dragonet80/MultiMicro/Base/ARE_entrenadora_modular_Arduino_mod.brd

## EAGLE design Base/ARE_entrenadora_modular_Arduino_mod.brd (2015-02-18)

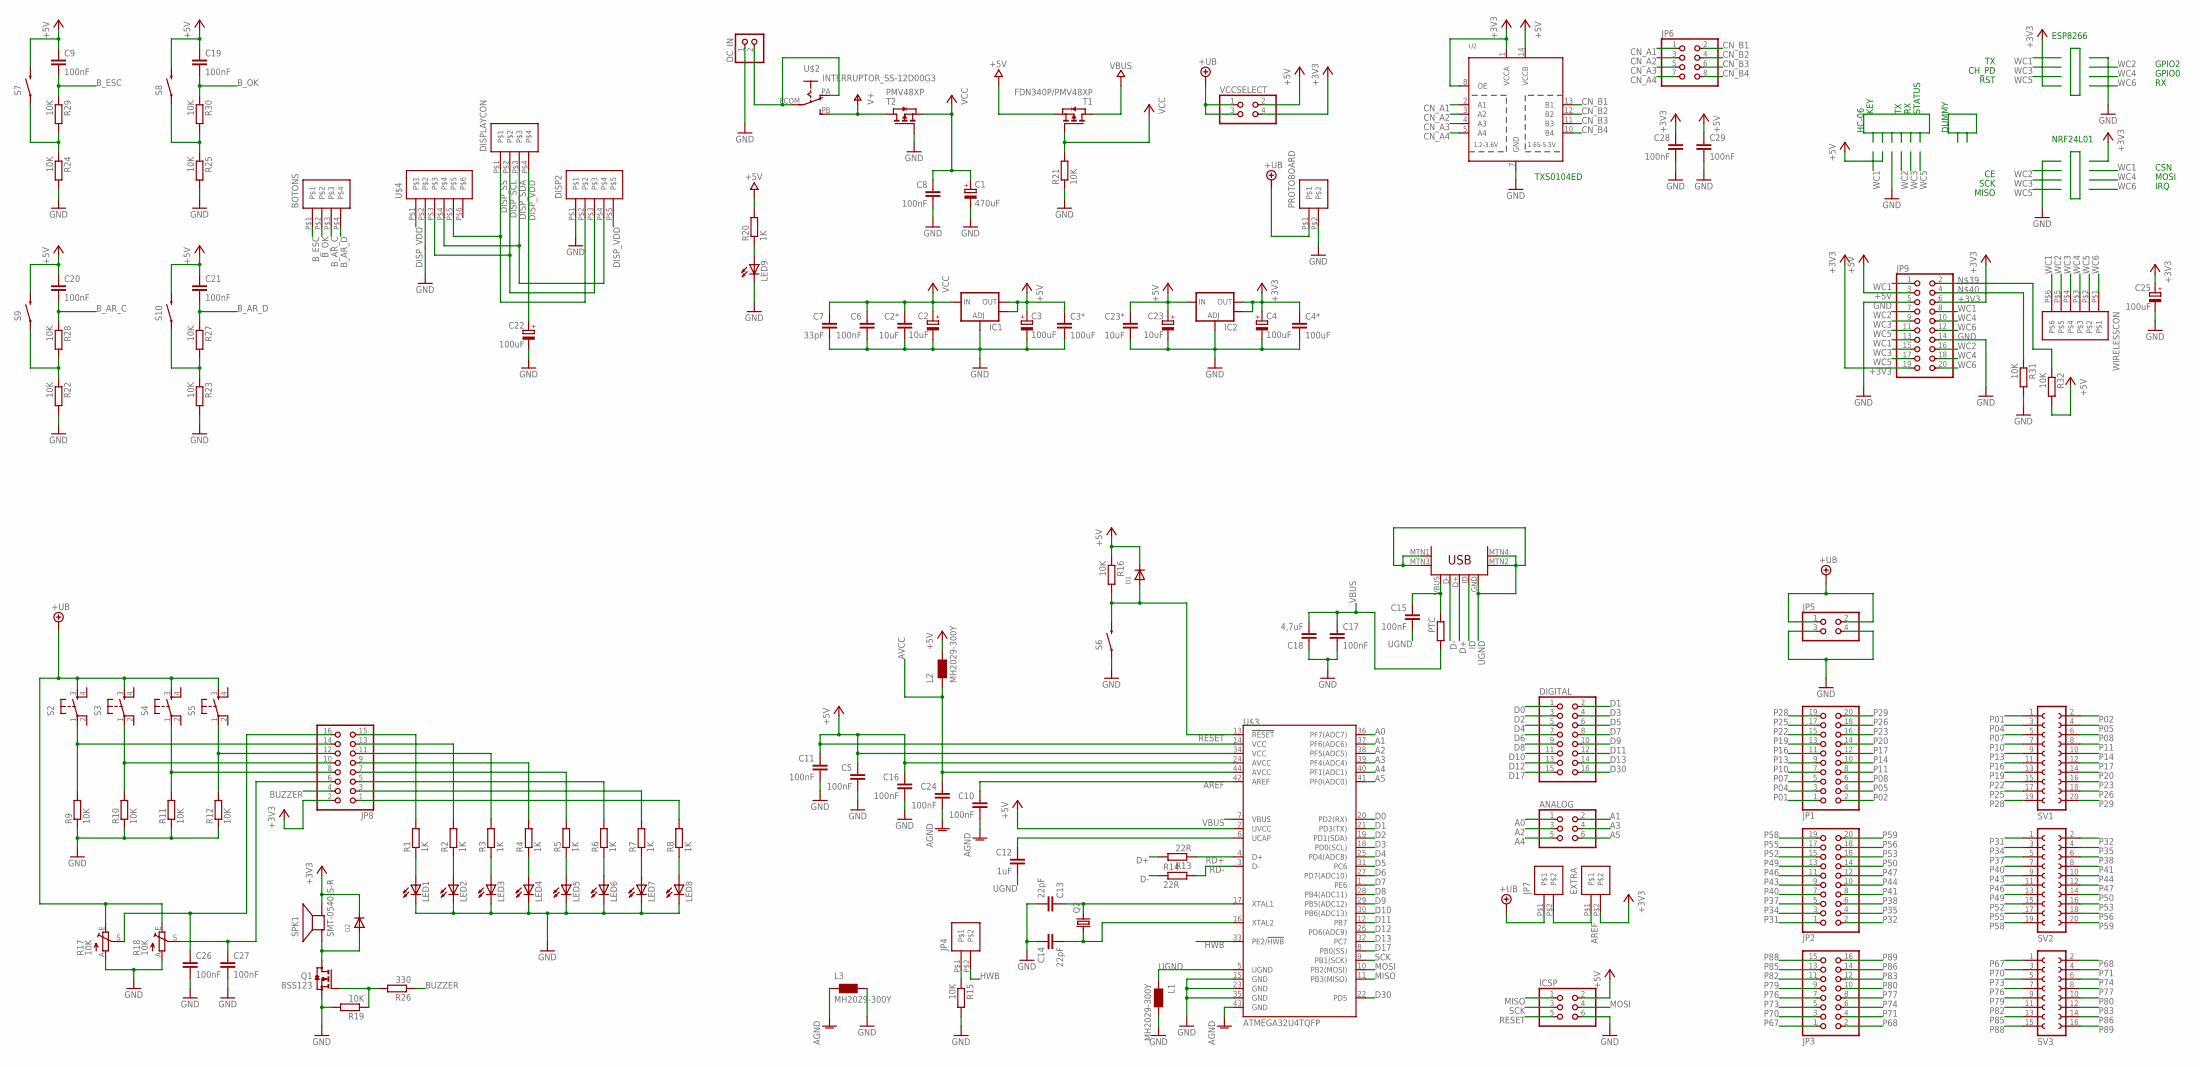
[picture p35: schematic ARE_entrenadora_modular_Arduino_mod.sch]

Parts:
ANALOG: PINHD-2X3; 2X03
BOTONS: PINHEAD_1X4; PINHEAD_1X4_2.54
C1: 470uF; E3,5-8
C2, C23: 10uF; SMC_C
C2*, C23*: 10uF; C1206
C3, C4: 100uF; CT7343
C3*, C4*: 100uF; C1206
C5, C6, C8, C9, C10, C11, C15, C16, C17, C19, C20, C21, C24, C26, C27, C28, C29: 100nF; C0805
C7: 33pF; C0805
C12: 1uF; C0805
C13, C14: 22pF; C0805
C18: 4,7uF; C0805
C22, C25: 100uF; SMC_C
D1, D2: DIODESOD-123; SOD-123
DC_IN: PINHD-1X2/90; 1X02/90
DIGITAL: PINHD-2X8; 2X08
DISP2: PINHEAD_1X5; PINHEAD_1X5_2.54
DISPLAYCON: PINHEAD_1X4; PINHEAD_1X4_2.54
EXTRA: PINHEAD_1X2; PINHEAD_1X2_2.54
IC1, IC2: V_REG_LM1117SOT223; SOT223
ICSP: PINHD-2X3; 2X03
JP1, JP2: PINHD-2X10/90; 2X10/90
JP3: PINHD-2X8/90; 2X08/90
JP4, JP7: PINHEAD_1X2; PINHEAD_1X2_2.54
JP5: PINHD-2X2/90; 2X02/90
JP6: PINHD-2X4; 2X04
JP8: PINHD-2X8; 2X08
JP9: PINHD-2X10; 2X10
L1, L2, L3: MH2029-300Y; 0805
LED1, LED2, LED3, LED4, LED5, LED6, LED7, LED8, LED9: LEDCHIP-LED0805; CHIP-LED0805
PROTOBOARD: PINHEAD_1X2; PINHEAD_1X2_2.54
PTC: R-EU_R1206; R1206
Q1: BSS123; SOT23
Q2: CRYSTALHC49UP; HC49UP
R1, R2, R3, R4, R5, R6, R7, R8, R20: 1K; R0805
R9, R10, R11, R12, R15, R16, R19, R21, R22, R23, R24, R25, R27, R28, R29, R30, R31, R32: 10K; R0805
R13, R14: 22R; R0805
R17, R18: 10K; CA6V
R26: 330; R0805
S2, S3, S4, S5: TAC_SWITCHPTH; TACTILE-PTH
S6, S7, S8, S9, S10: SWITCH-MOMENTARY-2-SMD-1101NE; TACTILE-SWITCH-1101NE
SPK1: SMT-0540-S-R
SV1, SV2: FE10-2
SV3: FE08-2
T1: FDN340P/PMV48XP; SOT-23
T2: PMV48XP; SOT-23
U2: TXB0104PWRSOIC14; SO14
U$1: USB-MINIB-5PIN; USB-MINIB
U$2: INTERRUPTOR_SS-12D00G3; SS-12D00G3
U$3: ATMEGA32U4TQFP; SPARKFUN-DIGITALIC_TQFP44
U$4: PINHEAD_1X6; PINHEAD_1X6_2.54
VCCSELECT: PINHD-2X2; 2X02
WIRELESSCON: PINHEAD_1X6; PINHEAD_1X6_2.54

Connections:
+3V3: C4.+, C4*.1, C25.+, C28.1, D2.C, EXTRA.P$2, IC2.2 (OUT), IC2.4 (OUT), JP8.2, JP9.6, JP9.19, SPK1.+ (-), U2.1 (VCCA), U2.8 (OE), VCCSELECT.4
+5V: C3.+, C3*.1, C5.1, C9.1, C11.1, C16.1, C19.1, C20.1, C21.1, C23.+, C23*.1, C29.1, D1.C, IC1.2 (OUT), IC1.4 (OUT), IC2.3 (IN), ICSP.2, JP9.3, L2.2, R16.1, R20.2, R32.2, S7.P$2 (2), S8.P$2 (2), S9.P$2 (2), S10.P$2 (2), T1.2 (S), U2.14 (VCCB), U$3.2 (UVCC), U$3.14 (VCC), U$3.24 (AVCC), U$3.34 (VCC), VCCSELECT.2
+UB: JP5.1, JP5.2, JP7.P$1, PROTOBOARD.P$1, R17.E, R18.E, S2.3, S3.3, S4.3, S5.3, VCCSELECT.1, VCCSELECT.3
A0: ANALOG.1, U$3.36 (PF7(ADC7))
A1: ANALOG.2, U$3.37 (PF6(ADC6))
A2: ANALOG.3, U$3.38 (PF5(ADC5))
A3: ANALOG.4, U$3.39 (PF4(ADC4))
A4: ANALOG.5, U$3.40 (PF1(ADC1))
A5: ANALOG.6, U$3.41 (PF0(ADC0))
AGND: C10.2, C24.2, L3.1, U$3.43 (GND)
AREF: C10.1, EXTRA.P$1, JP7.P$2, U$3.42 (AREF)
AVCC: C24.1, L2.1, U$3.44 (AVCC)
BUZZER: JP8.4, R26.1
B_AR_C: BOTONS.P$3, C20.2, R28.1
B_AR_D: BOTONS.P$4, C21.2, R27.1
B_ESC: BOTONS.P$1, C9.2, R29.1
B_OK: BOTONS.P$2, C19.2, R30.1
CN_A1: JP6.1, U2.2 (A1)
CN_A2: JP6.3, U2.3 (A2)
CN_A3: JP6.5, U2.4 (A3)
CN_A4: JP6.7, U2.5 (A4)
CN_B1: JP6.2, U2.13 (B1)
CN_B2: JP6.4, U2.12 (B2)
CN_B3: JP6.6, U2.11 (B3)
CN_B4: JP6.8, U2.10 (B4)
D0: DIGITAL.1, U$3.20 (PD2(RX))
D1: DIGITAL.2, U$3.21 (PD3(TX))
D2: DIGITAL.3, U$3.19 (PD1(SDA))
D3: DIGITAL.4, U$3.18 (PD0(SCL))
D4: DIGITAL.5, U$3.25 (PD4(ADC8))
D5: DIGITAL.6, U$3.31 (PC6)
D6: DIGITAL.7, U$3.27 (PD7(ADC10))
D7: DIGITAL.8, U$3.1 (PE6)
D8: DIGITAL.9, U$3.28 (PB4(ADC11))
D9: DIGITAL.10, U$3.29 (PB5(ADC12))
D10: DIGITAL.11, U$3.30 (PB6(ADC13))
D11: DIGITAL.12, U$3.12 (PB7)
D12: DIGITAL.13, U$3.26 (PD6(ADC9))
D13: DIGITAL.14, U$3.32 (PC7)
D17: DIGITAL.15, U$3.8 (PB0(SS))
D30: DIGITAL.16, U$3.22 (PD5)
D+: R13.2, U$1.D+
D-: R14.1, U$1.D-
DISP_SCL: DISP2.P$3, DISPLAYCON.P$2, U$4.P$3
DISP_SDA: DISP2.P$4, DISPLAYCON.P$3, U$4.P$4
DISP_SS: DISP2.P$2, DISPLAYCON.P$1, U$4.P$5
DISP_VDD: C22.+, DISP2.P$5, DISPLAYCON.P$4, U$4.P$1
GND: C1.-, C2.-, C2*.2, C3.-, C3*.2, C4.-, C4*.2, C5.2, C6.2, C7.2, C8.2, C11.2, C13.2, C14.1, C16.2, C17.2, C18.1, C22.-, C23.-, C23*.2, C25.-, C26.2, C27.2, C28.2, C29.2, DC_IN.1, DISP2.P$1, IC1.1 (ADJ), IC2.1 (ADJ), ICSP.6, JP5.3, JP5.4, JP9.5, JP9.14, L1.2, L3.2, LED1.C, LED2.C, LED3.C, LED4.C, LED5.C, LED6.C, LED7.C, LED8.C, LED9.C, PROTOBOARD.P$2, Q1.2 (S), R9.1, R10.1, R11.1, R12.1, R15.2, R17.A, R18.A, R19.2, R21.1, R22.2, R23.2, R24.2, R25.2, R31.2, S6.P$1 (1), T2.3 (G), U2.7 (GND), U$3.15 (GND), U$3.23 (GND), U$3.35 (GND), U$4.P$2
HWB: JP4.P$2, U$3.33 (PE2/!HWB)
ID: U$1.ID
MISO: ICSP.1, U$3.11 (PB3(MISO))
MOSFET_BASE: Q1.1 (G), R19.1, R26.2
MOSI: ICSP.4, U$3.10 (PB2(MOSI))
unnamed: LED1.A, R1.1
unnamed: LED2.A, R2.1
unnamed: LED3.A, R3.1
unnamed: LED4.A, R4.1
unnamed: JP8.13, R2.2
unnamed: JP8.11, R3.2
unnamed: JP8.15, R1.2
unnamed: JP8.9, R4.2
unnamed: LED9.A, R20.1
unnamed: C27.1, JP8.6, R18.S
unnamed: D2.A, Q1.3 (D), SPK1.- (+)
unnamed: JP4.P$1, R15.1
unnamed: C13.1, Q2.2, U$3.17 (XTAL1)
unnamed: C14.2, Q2.1, U$3.16 (XTAL2)
unnamed: R22.1, R28.2, S9.P$1 (1)
unnamed: JP8.8, R11.2, S4.1
unnamed: JP8.12, R12.2, S5.1
unnamed: C15.1, PTC.1, U$1.VBUS
unnamed: R24.1, R29.2, S7.P$1 (1)
unnamed: LED5.A, R5.1
unnamed: R25.1, R30.2, S8.P$1 (1)
unnamed: JP8.10, R10.2, S3.1
unnamed: R23.1, R27.2, S10.P$1 (1)
unnamed: C12.1, U$3.6 (UCAP)
unnamed: JP9.2, R32.1
unnamed: JP9.4, R31.1
unnamed: DC_IN.2, U$2.PA, U$2.PCOM
unnamed: LED6.A, R6.1
unnamed: LED7.A, R7.1
unnamed: LED8.A, R8.1
unnamed: JP8.14, R9.2, S2.1
unnamed: C26.1, JP8.16, R17.S
unnamed: JP8.5, R6.2
unnamed: JP8.3, R7.2
unnamed: JP8.7, R5.2
unnamed: JP8.1, R8.2
P01: JP1.1, SV1.1
P02: JP1.2, SV1.2
P04: JP1.3, SV1.3
P05: JP1.4, SV1.4
P07: JP1.5, SV1.5
P08: JP1.6, SV1.6
P10: JP1.7, SV1.7
P11: JP1.8, SV1.8
P13: JP1.9, SV1.9
P14: JP1.10, SV1.10
P16: JP1.11, SV1.11
P17: JP1.12, SV1.12
P19: JP1.13, SV1.13
P20: JP1.14, SV1.14
P22: JP1.15, SV1.15
P23: JP1.16, SV1.16
P25: JP1.17, SV1.17
P26: JP1.18, SV1.18
P28: JP1.19, SV1.19
P29: JP1.20, SV1.20
P31: JP2.1, SV2.1
P32: JP2.2, SV2.2
P34: JP2.3, SV2.3
P35: JP2.4, SV2.4
P37: JP2.5, SV2.5
P38: JP2.6, SV2.6
P40: JP2.7, SV2.7
P41: JP2.8, SV2.8
P43: JP2.9, SV2.9
P44: JP2.10, SV2.10
P46: JP2.11, SV2.11
P47: JP2.12, SV2.12
P49: JP2.13, SV2.13
P50: JP2.14, SV2.14
P52: JP2.15, SV2.15
P53: JP2.16, SV2.16
P55: JP2.17, SV2.17
P56: JP2.18, SV2.18
P58: JP2.19, SV2.19
P59: JP2.20, SV2.20
P67: JP3.1, SV3.1
P68: JP3.2, SV3.2
P70: JP3.3, SV3.3
P71: JP3.4, SV3.4
P73: JP3.5, SV3.5
P74: JP3.6, SV3.6
P76: JP3.7, SV3.7
P77: JP3.8, SV3.8
P79: JP3.9, SV3.9
P80: JP3.10, SV3.10
P82: JP3.11, SV3.11
P83: JP3.12, SV3.12
P85: JP3.13, SV3.13
P86: JP3.14, SV3.14
P88: JP3.15, SV3.15
P89: JP3.16, SV3.16
RD+: R13.1, U$3.4 (D+)
RD-: R14.2, U$3.3 (D-)
RESET: D1.A, ICSP.5, R16.2, S6.P$2 (2), U$3.13 (!RESET)
SCK: ICSP.3, U$3.9 (PB1(SCK))
UGND: C12.2, C15.2, L1.1, U$1.GND, U$1.MTN1 (MTN2), U$1.MTN2 (MTN3), U$1.MTN3 (MTN1), U$1.MTN4, U$3.5 (UGND)
V+: T2.1 (D), U$2.PB
VBUS: C17.1, C18.2, PTC.2, T1.1 (D), U$3.7 (VBUS)
VCC: C1.+, C2.+, C2*.1, C6.1, C7.1, C8.1, IC1.3 (IN), R21.2, T1.3 (G), T2.2 (S)
WC1: JP9.1, JP9.8, JP9.13, WIRELESSCON.P$6
WC2: JP9.7, JP9.16, WIRELESSCON.P$5
WC3: JP9.9, JP9.15, WIRELESSCON.P$4
WC4: JP9.10, JP9.18, WIRELESSCON.P$3
WC5: JP9.11, JP9.17, WIRELESSCON.P$2
WC6: JP9.12, JP9.20, WIRELESSCON.P$1

Notes on the sheet:
TXS0104ED
KEY
STATUS
CH_PD
RST
SCK
MISO
GPIO2
GPIO0
CSN
MOSI
IRQ
HC-06
DUMMY
NRF24L01
ESP8266

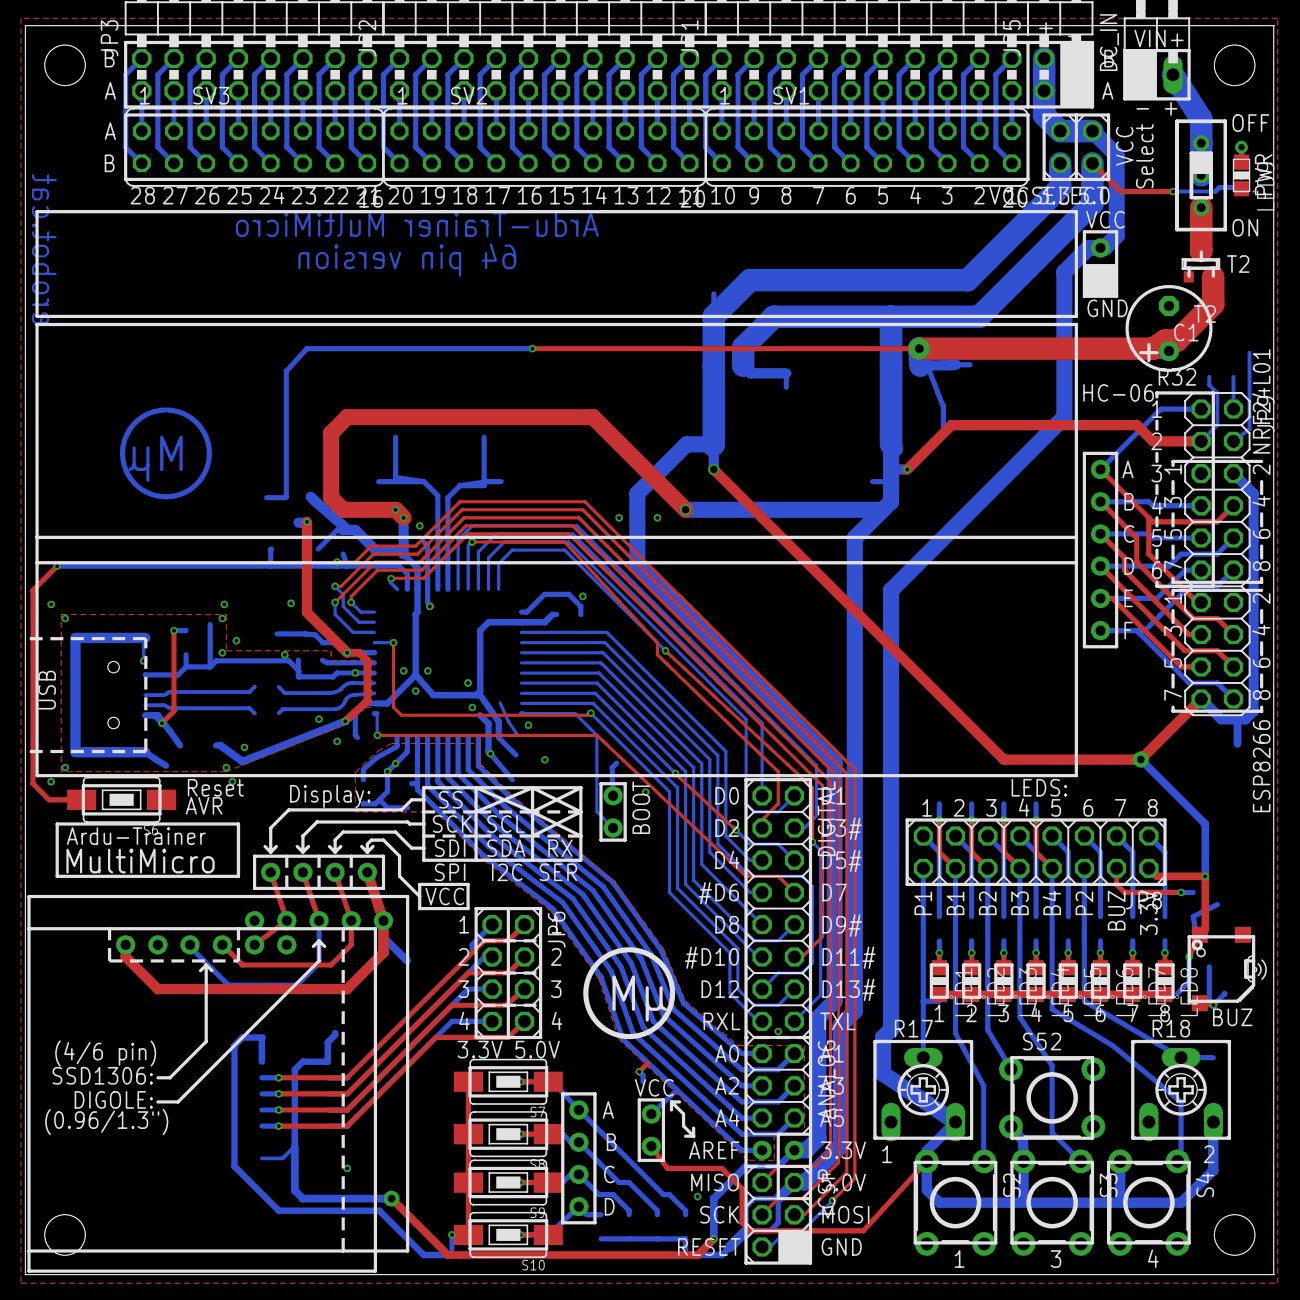
[picture p36: board ARE_entrenadora_modular_Arduino_mod.brd from above]

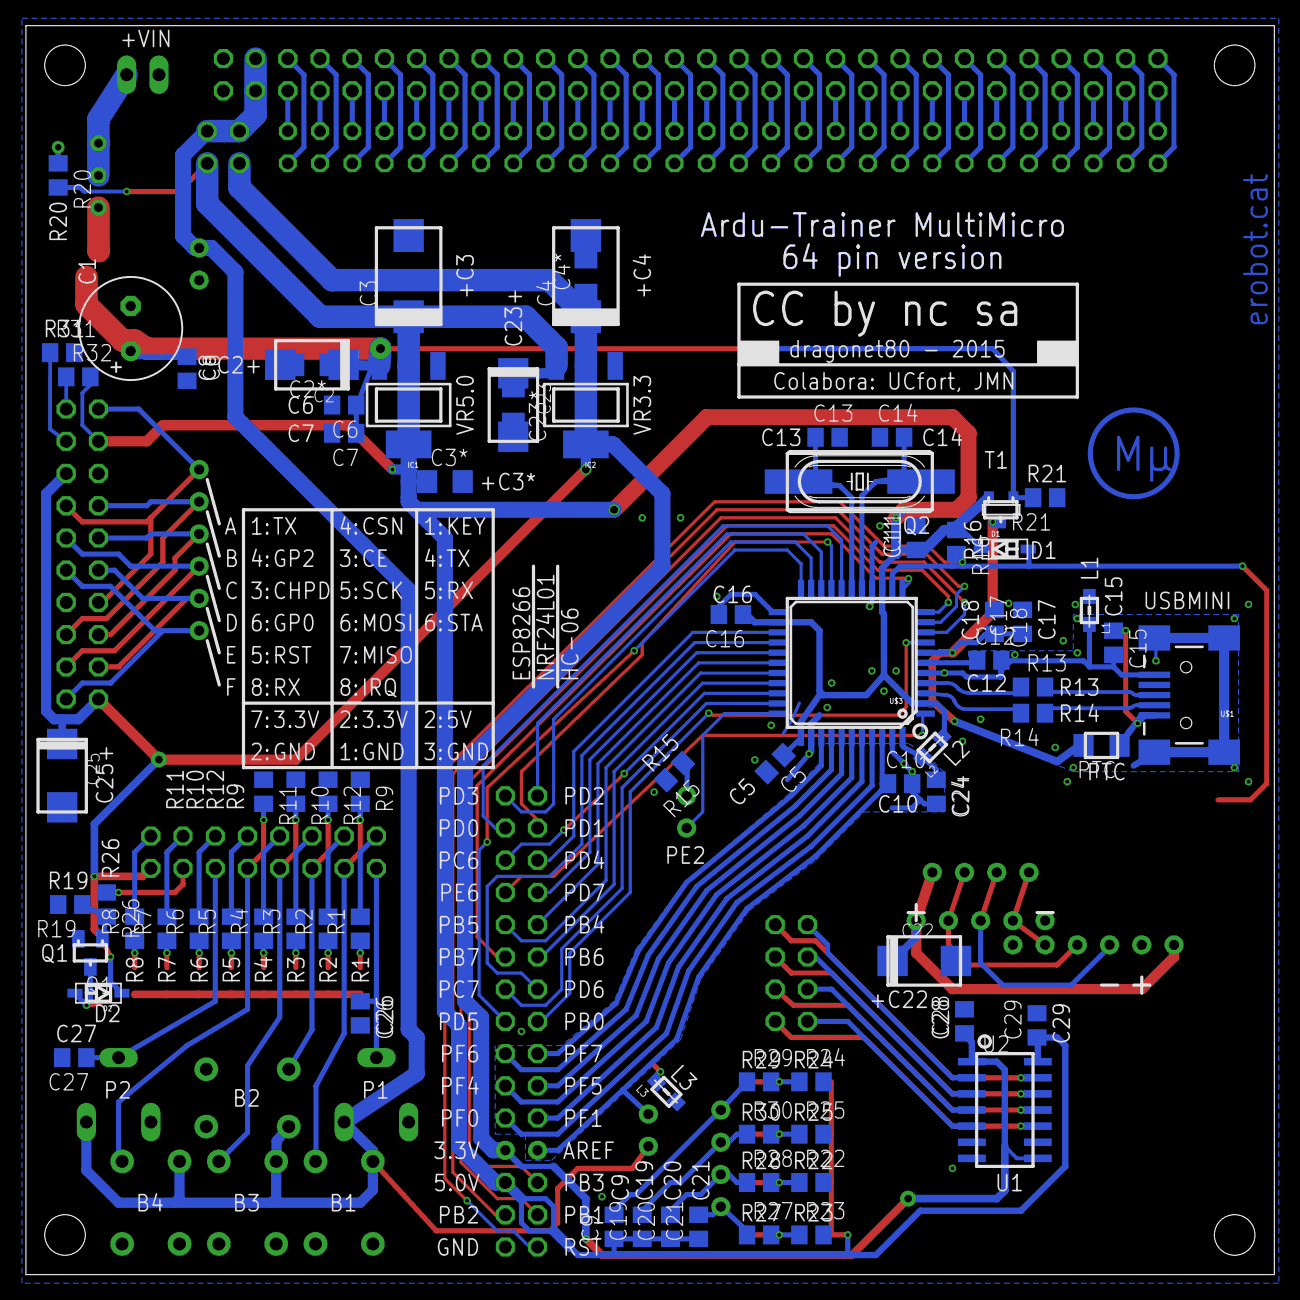
[picture p37: board ARE_entrenadora_modular_Arduino_mod.brd from below]

Board: 2 copper layers, 98.4 x 98.5 mm, 124 parts (77 on the bottom side), 158 nets.
