dragonet80/MultiMicro/Adaptadores/Microchip/ARE_adaptadora_PIC_44pin.brd

## EAGLE design Adaptadores/Microchip/ARE_adaptadora_PIC_44pin.brd (2015-02-18)

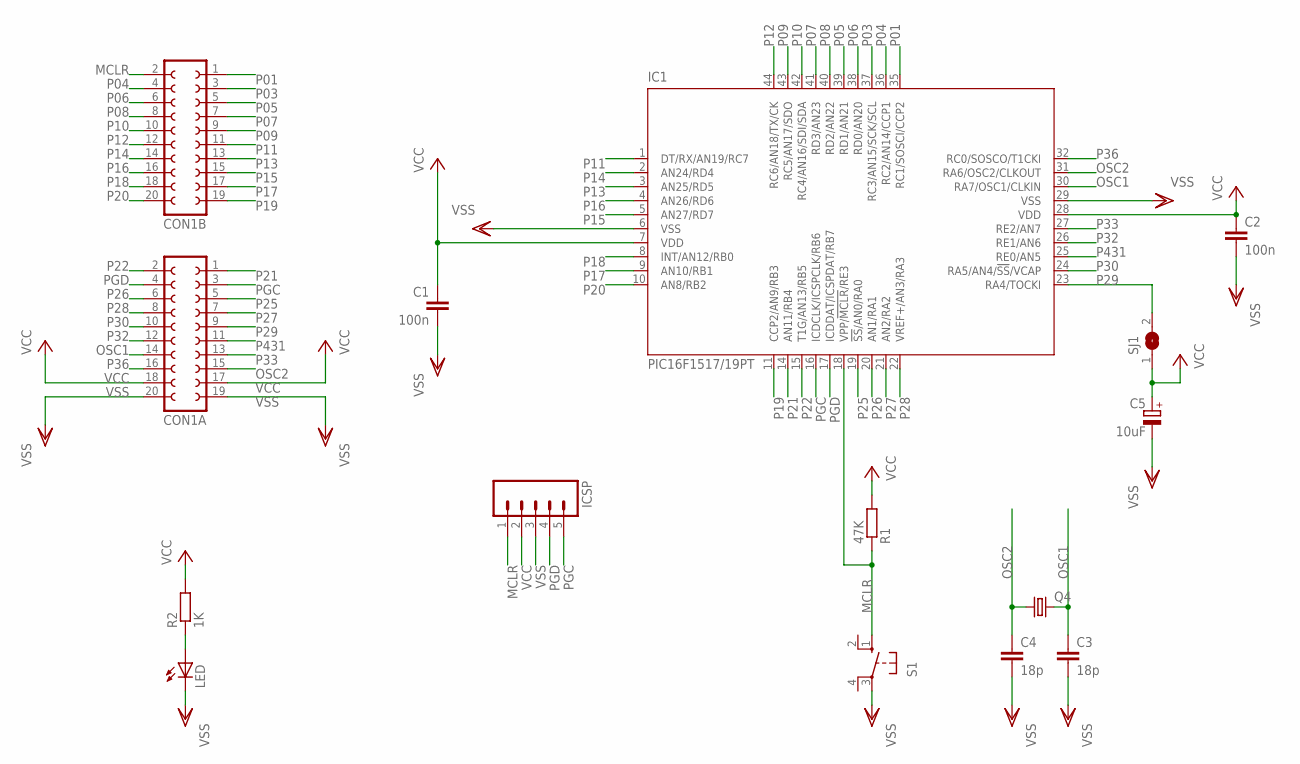
[picture p38: schematic ARE_adaptadora_PIC_44pin.sch, PIC 16F / 18F 44 pin]

Parts:
C1, C2: 100n; C0805
C3, C4: 18p; C0805
C5: 10uF; SMC_C
CON1A, CON1B: FE10-2W
IC1: PIC16F1517/19PT; TQFP44
ICSP: M05PTH; 1X05
LED: LEDCHIPLED_0805; CHIPLED_0805
Q4: CRYSTALHC18U-V; HC18U-V
R1: 47K; R0805
R2: 1K; R0805
S1: 10-XX; B3F-10XX; MPN B3F-1000
SJ1: SJ

Connections:
MCLR: CON1B.2, IC1.18 (VPP/!MCLR!/RE3), ICSP.1, R1.1, S1.1 (S)
unnamed: LED.A, R2.1
OSC1: C3.1, CON1A.14, IC1.30 (RA7/OSC1/CLKIN), Q4.2
OSC2: C4.1, CON1A.15, IC1.31 (RA6/OSC2/CLKOUT), Q4.1
P01: CON1B.1, IC1.35 (RC1/SOSCI/CCP2)
P03: CON1B.3, IC1.37 (RC3/AN15/SCK/SCL)
P04: CON1B.4, IC1.36 (RC2/AN14/CCP1)
P05: CON1B.5, IC1.39 (RD1/AN21)
P06: CON1B.6, IC1.38 (RD0/AN20)
P07: CON1B.7, IC1.41 (RD3/AN23)
P08: CON1B.8, IC1.40 (RD2/AN22)
P09: CON1B.9, IC1.43 (RC5/AN17/SDO)
P10: CON1B.10, IC1.42 (RC4/AN16/SDI/SDA)
P11: CON1B.11, IC1.1 (DT/RX/AN19/RC7)
P12: CON1B.12, IC1.44 (RC6/AN18/TX/CK)
P13: CON1B.13, IC1.3 (AN25/RD5)
P14: CON1B.14, IC1.2 (AN24/RD4)
P15: CON1B.15, IC1.5 (AN27/RD7)
P16: CON1B.16, IC1.4 (AN26/RD6)
P17: CON1B.17, IC1.9 (AN10/RB1)
P18: CON1B.18, IC1.8 (INT/AN12/RB0)
P19: CON1B.19, IC1.11 (CCP2/AN9/RB3)
P20: CON1B.20, IC1.10 (AN8/RB2)
P21: CON1A.1, IC1.14 (AN11/RB4)
P22: CON1A.2, IC1.15 (T1G/AN13/RB5)
P25: CON1A.5, IC1.19 (!SS!/AN0/RA0)
P26: CON1A.6, IC1.20 (AN1/RA1)
P27: CON1A.7, IC1.21 (AN2/RA2)
P28: CON1A.8, IC1.22 (VREF+/AN3/RA3)
P29: CON1A.9, IC1.23 (RA4/TOCKI), SJ1.2
P30: CON1A.10, IC1.24 (RA5/AN4/!SS!/VCAP)
P32: CON1A.12, IC1.26 (RE1/AN6)
P33: CON1A.13, IC1.27 (RE2/AN7)
P36: CON1A.16, IC1.32 (RC0/SOSCO/T1CKI)
P431: CON1A.11, IC1.25 (RE0/AN5)
PGC: CON1A.3, IC1.16 (ICDCLK/ICSPCLK/RB6), ICSP.5
PGD: CON1A.4, IC1.17 (ICDDAT/ICSPDAT/RB7), ICSP.4
VCC: C1.1, C2.1, C5.+, CON1A.17, CON1A.18, IC1.7 (VDD), IC1.28 (VDD), ICSP.2, R1.2, R2.2, SJ1.1
VSS: C1.2, C2.2, C3.2, C4.2, C5.-, CON1A.19, CON1A.20, IC1.6 (VSS), IC1.29 (VSS), ICSP.3, LED.C, S1.3

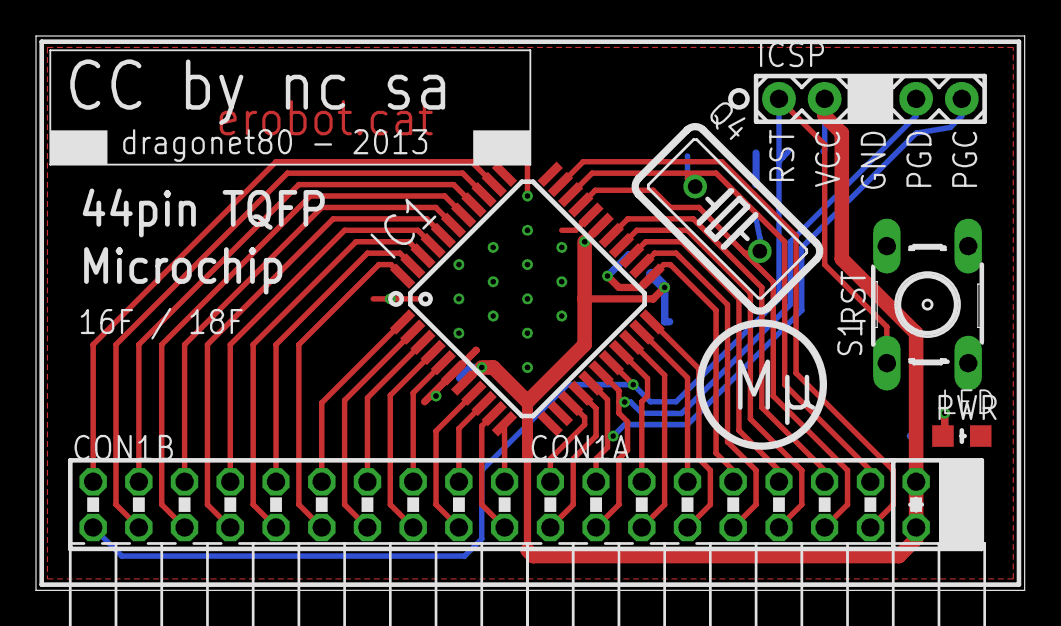
[picture p39: board ARE_adaptadora_PIC_44pin.brd from above]

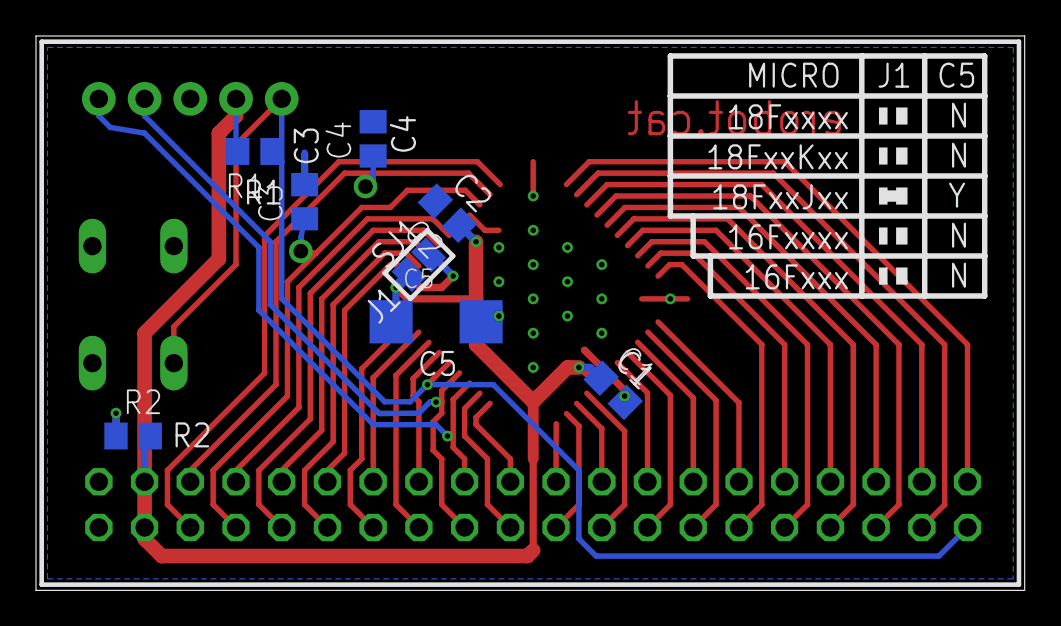
[picture p40: board ARE_adaptadora_PIC_44pin.brd from below]

Board: 2 copper layers, 54.9 x 30.8 mm, 15 parts (8 on the bottom side), 39 nets.
