dragonet80/MultiMicro/Adaptadores/Microchip/ARE_adaptadora_PIC_28pin.brd

## EAGLE design Adaptadores/Microchip/ARE_adaptadora_PIC_28pin.brd (2015-02-18)

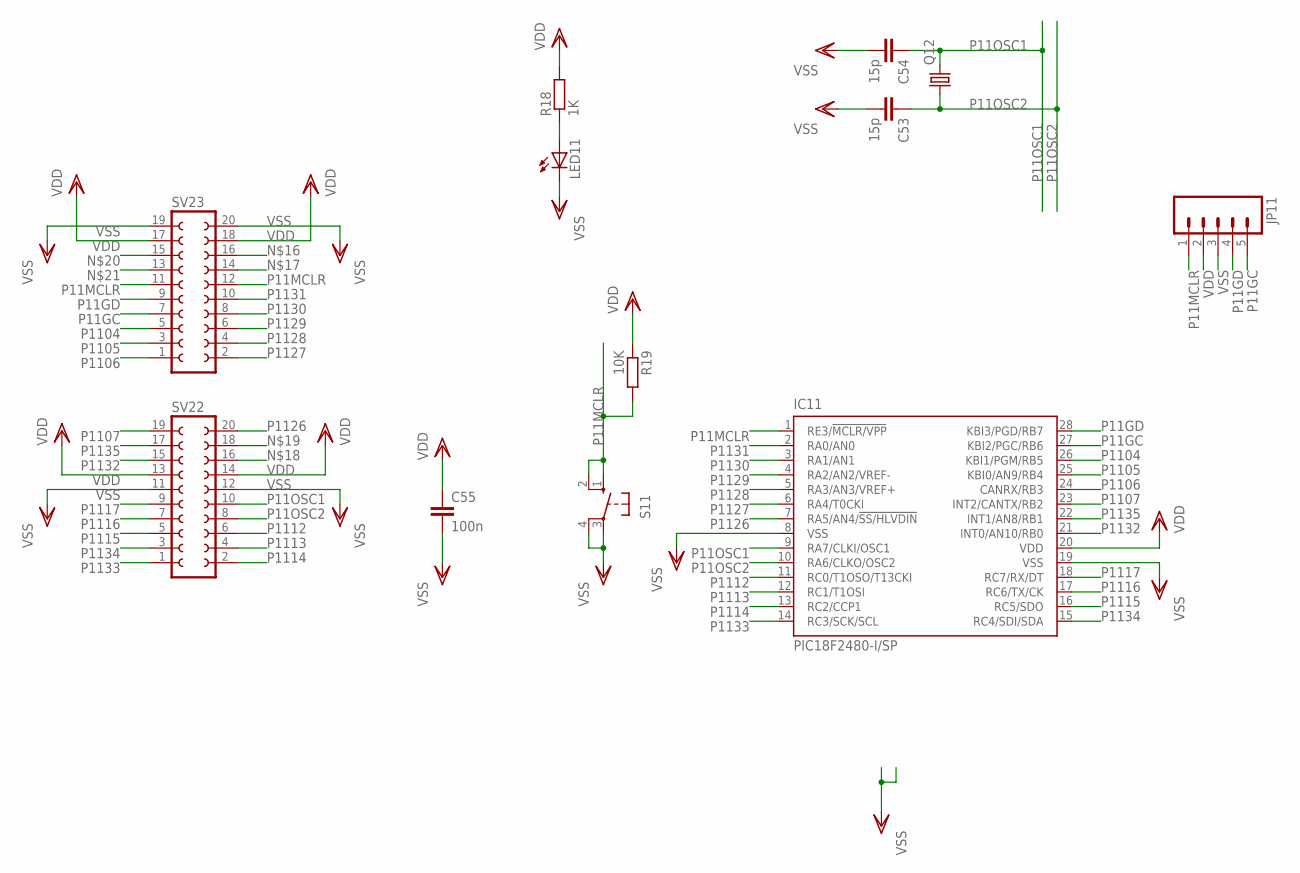
[picture p41: schematic ARE_adaptadora_PIC_28pin.sch, 16F/18F 28 pin DIP]

Parts:
C53, C54: 15p; C0805
C55: 100n; C0805
IC11: PIC18F2480-I/SP; DIL28-3
JP11: M05PTH; 1X05
LED11: LED3MM
Q12: CRYSTALHC18U-V; HC18U-V
R18: 1K; R0805
R19: 10K; R0805
S11: 10-XX; B3F-10XX; MPN B3F-1000
SV22, SV23: FE10-2W

Connections:
unnamed: LED11.A, R18.1
P11GC: IC11.27 (KBI2/PGC/RB6), JP11.5, SV23.7
P11GD: IC11.28 (KBI3/PGD/RB7), JP11.4, SV23.9
P11MCLR: IC11.1 (RE3/!MCLR/VPP), JP11.1, R19.2, S11.1 (S), S11.2 (S1), SV23.11, SV23.12
P11OSC1: C54.1, IC11.9 (RA7/CLKI/OSC1), Q12.2, SV22.10
P11OSC2: C53.1, IC11.10 (RA6/CLKO/OSC2), Q12.1, SV22.8
P1104: IC11.26 (KBI1/PGM/RB5), SV23.5
P1105: IC11.25 (KBI0/AN9/RB4), SV23.3
P1106: IC11.24 (CANRX/RB3), SV23.1
P1107: IC11.23 (INT2/CANTX/RB2), SV22.19
P1112: IC11.11 (RC0/T1OSO/T13CKI), SV22.6
P1113: IC11.12 (RC1/T1OSI), SV22.4
P1114: IC11.13 (RC2/CCP1), SV22.2
P1115: IC11.16 (RC5/SDO), SV22.5
P1116: IC11.17 (RC6/TX/CK), SV22.7
P1117: IC11.18 (RC7/RX/DT), SV22.9
P1126: IC11.7 (RA5/AN4/!SS/HLVDIN), SV22.20
P1127: IC11.6 (RA4/T0CKI), SV23.2
P1128: IC11.5 (RA3/AN3/VREF+), SV23.4
P1129: IC11.4 (RA2/AN2/VREF-), SV23.6
P1130: IC11.3 (RA1/AN1), SV23.8
P1131: IC11.2 (RA0/AN0), SV23.10
P1132: IC11.21 (INT0/AN10/RB0), SV22.15
P1133: IC11.14 (RC3/SCK/SCL), SV22.1
P1134: IC11.15 (RC4/SDI/SDA), SV22.3
P1135: IC11.22 (INT1/AN8/RB1), SV22.17
VDD: C55.1, IC11.20 (VDD), JP11.2, R18.2, R19.1, SV22.13, SV22.14, SV23.17, SV23.18
VSS: C53.2, C54.2, C55.2, IC11.8 (VSS), IC11.19 (VSS), JP11.3, LED11.K (C), S11.3, S11.4 (P1), SV22.11, SV22.12, SV23.19, SV23.20

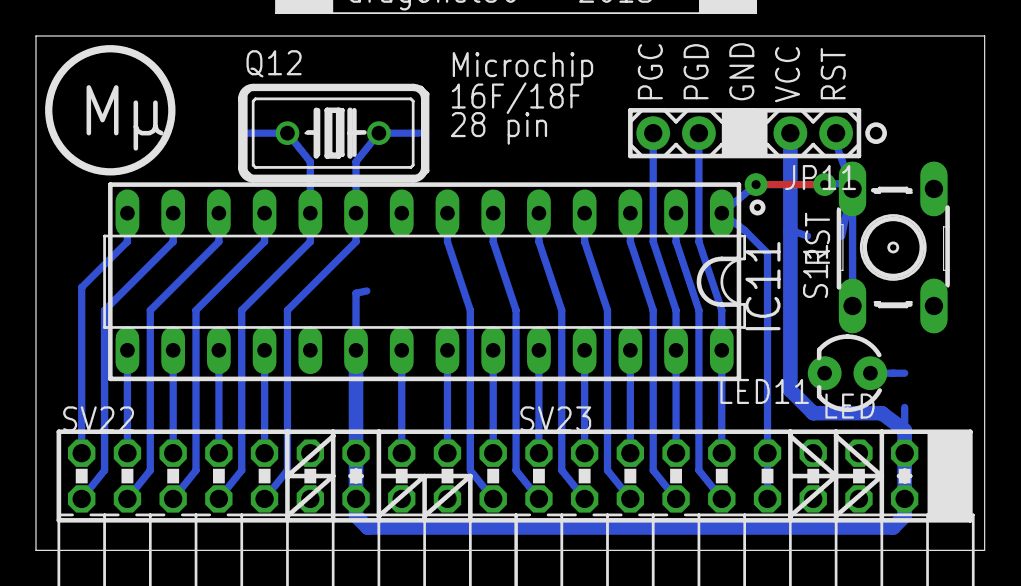
[picture p42: board ARE_adaptadora_PIC_28pin.brd from above]

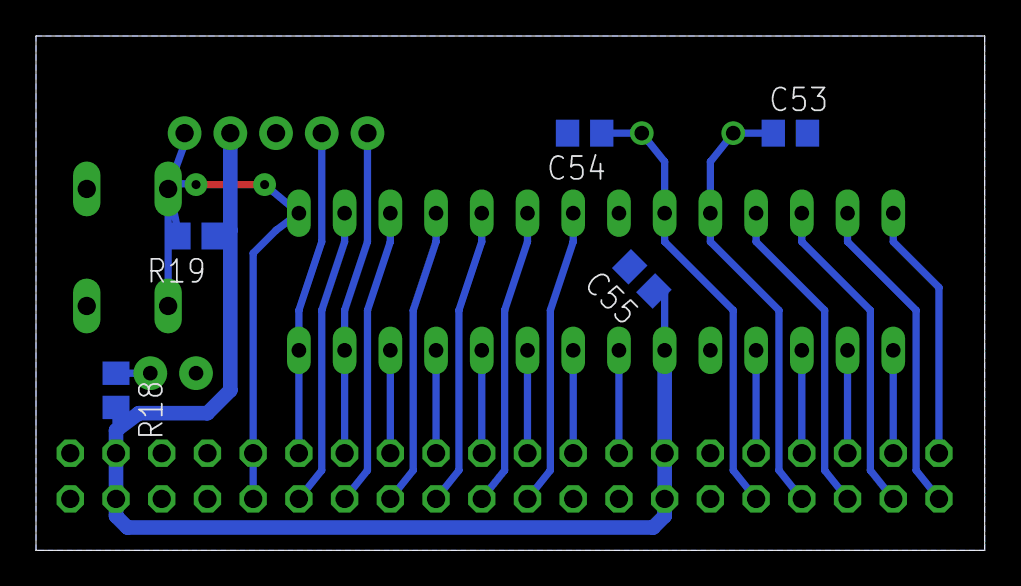
[picture p43: board ARE_adaptadora_PIC_28pin.brd from below]

Board: 2 copper layers, 52.7 x 28.6 mm, 12 parts (5 on the bottom side), 28 nets.
