dragonet80/MultiMicro/Adaptadores/ARE_adaptadores_final.brd

## EAGLE design Adaptadores/_OLD_/ARE_adaptadores_final.brd (2013-03-19, an earlier design)

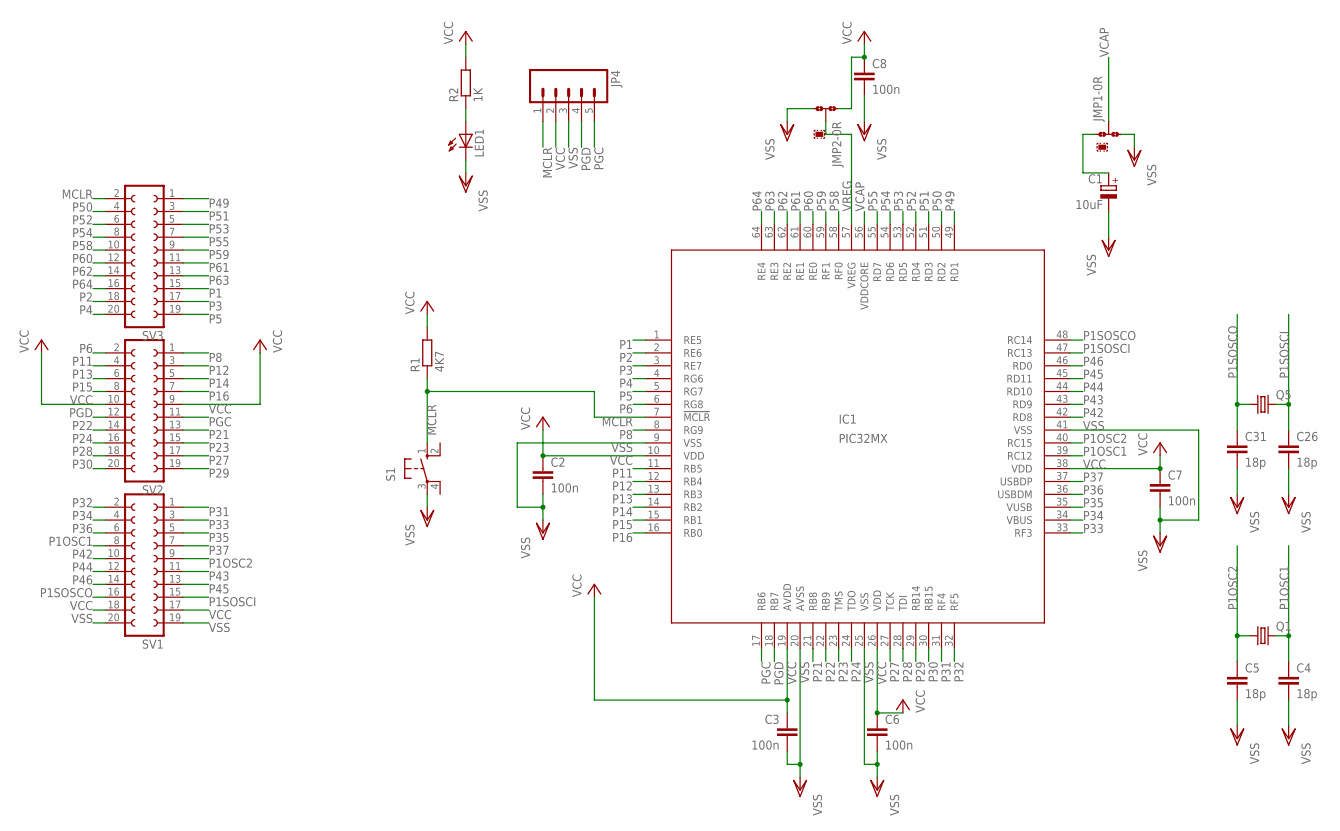
[picture p44: schematic ARE_adaptadores_final.sch, sheet 1, dsPIC / 24F / PIC32 64pin]

Parts:
C1: 10uF; SMC_C
C2, C3, C6, C7, C8: 100n; C0805
C4, C5, C26, C31: 18p; C0805
IC1: PIC32MX; TQFP64-10X10
JMP1, JMP2: 0R-JUMPA; A0R-JMP
JP4: M05PTH; 1X05
LED1: LEDCHIPLED_0805; CHIPLED_0805
Q1, Q5: CRYSTALHC18U-V; HC18U-V
R1: 4K7; R0805
R2: 1K; R0805
S1: 10-XX; B3F-10XX; MPN B3F-1000
SV1, SV2, SV3: FE10-2W

Connections:
MCLR: IC1.7 (!MCLR), JP4.1, R1.1, S1.1 (S), SV3.2
unnamed: LED1.A, R2.1
unnamed: C1.+, JMP1.1
P1: IC1.1 (RE5), SV3.15
P1OSC1: C4.1, IC1.39 (RC12), Q1.2, SV1.8
P1OSC2: C5.1, IC1.40 (RC15), Q1.1, SV1.9
P1SOSCI: C26.1, IC1.47 (RC13), Q5.2, SV1.15
P1SOSCO: C31.1, IC1.48 (RC14), Q5.1, SV1.16
P2: IC1.2 (RE6), SV3.18
P3: IC1.3 (RE7), SV3.17
P4: IC1.4 (RG6), SV3.20
P5: IC1.5 (RG7), SV3.19
P6: IC1.6 (RG8), SV2.2
P8: IC1.8 (RG9), SV2.1
P11: IC1.11 (RB5), SV2.4
P12: IC1.12 (RB4), SV2.3
P13: IC1.13 (RB3), SV2.6
P14: IC1.14 (RB2), SV2.5
P15: IC1.15 (RB1), SV2.8
P16: IC1.16 (RB0), SV2.7
P21: IC1.21 (RB8), SV2.13
P22: IC1.22 (RB9), SV2.14
P23: IC1.23 (TMS), SV2.15
P24: IC1.24 (TDO), SV2.16
P27: IC1.27 (TCK), SV2.17
P28: IC1.28 (TDI), SV2.18
P29: IC1.29 (RB14), SV2.19
P30: IC1.30 (RB15), SV2.20
P31: IC1.31 (RF4), SV1.1
P32: IC1.32 (RF5), SV1.2
P33: IC1.33 (RF3), SV1.3
P34: IC1.34 (VBUS), SV1.4
P35: IC1.35 (VUSB), SV1.5
P36: IC1.36 (USBDM), SV1.6
P37: IC1.37 (USBDP), SV1.7
P42: IC1.42 (RD8), SV1.10
P43: IC1.43 (RD9), SV1.11
P44: IC1.44 (RD10), SV1.12
P45: IC1.45 (RD11), SV1.13
P46: IC1.46 (RD0), SV1.14
P49: IC1.49 (RD1), SV3.1
P50: IC1.50 (RD2), SV3.4
P51: IC1.51 (RD3), SV3.3
P52: IC1.52 (RD4), SV3.6
P53: IC1.53 (RD5), SV3.5
P54: IC1.54 (RD6), SV3.8
P55: IC1.55 (RD7), SV3.7
P58: IC1.58 (RF0), SV3.10
P59: IC1.59 (RF1), SV3.9
P60: IC1.60 (RE0), SV3.12
P61: IC1.61 (RE1), SV3.11
P62: IC1.62 (RE2), SV3.14
P63: IC1.63 (RE3), SV3.13
P64: IC1.64 (RE4), SV3.16
PGC: IC1.17 (RB6), JP4.5, SV2.11
PGD: IC1.18 (RB7), JP4.4, SV2.12
VCAP: IC1.56 (VDDCORE), JMP1.2
VCC: C2.1, C3.1, C6.1, C7.1, C8.1, IC1.10 (VDD), IC1.19 (AVDD), IC1.26 (VDD), IC1.38 (VDD), JMP2.1, JP4.2, R1.2, R2.2, SV1.17, SV1.18, SV2.9, SV2.10; also elsewhere on the board
VREG: IC1.57 (VREG), JMP2.2
VSS: C1.-, C2.2, C3.2, C4.2, C5.2, C6.2, C7.2, C8.2, C26.2, C31.2, IC1.9 (VSS), IC1.20 (AVSS), IC1.25 (VSS), IC1.41 (VSS), JMP1.3, JMP2.3, JP4.3, LED1.C, S1.3, SV1.19, SV1.20; also elsewhere on the board

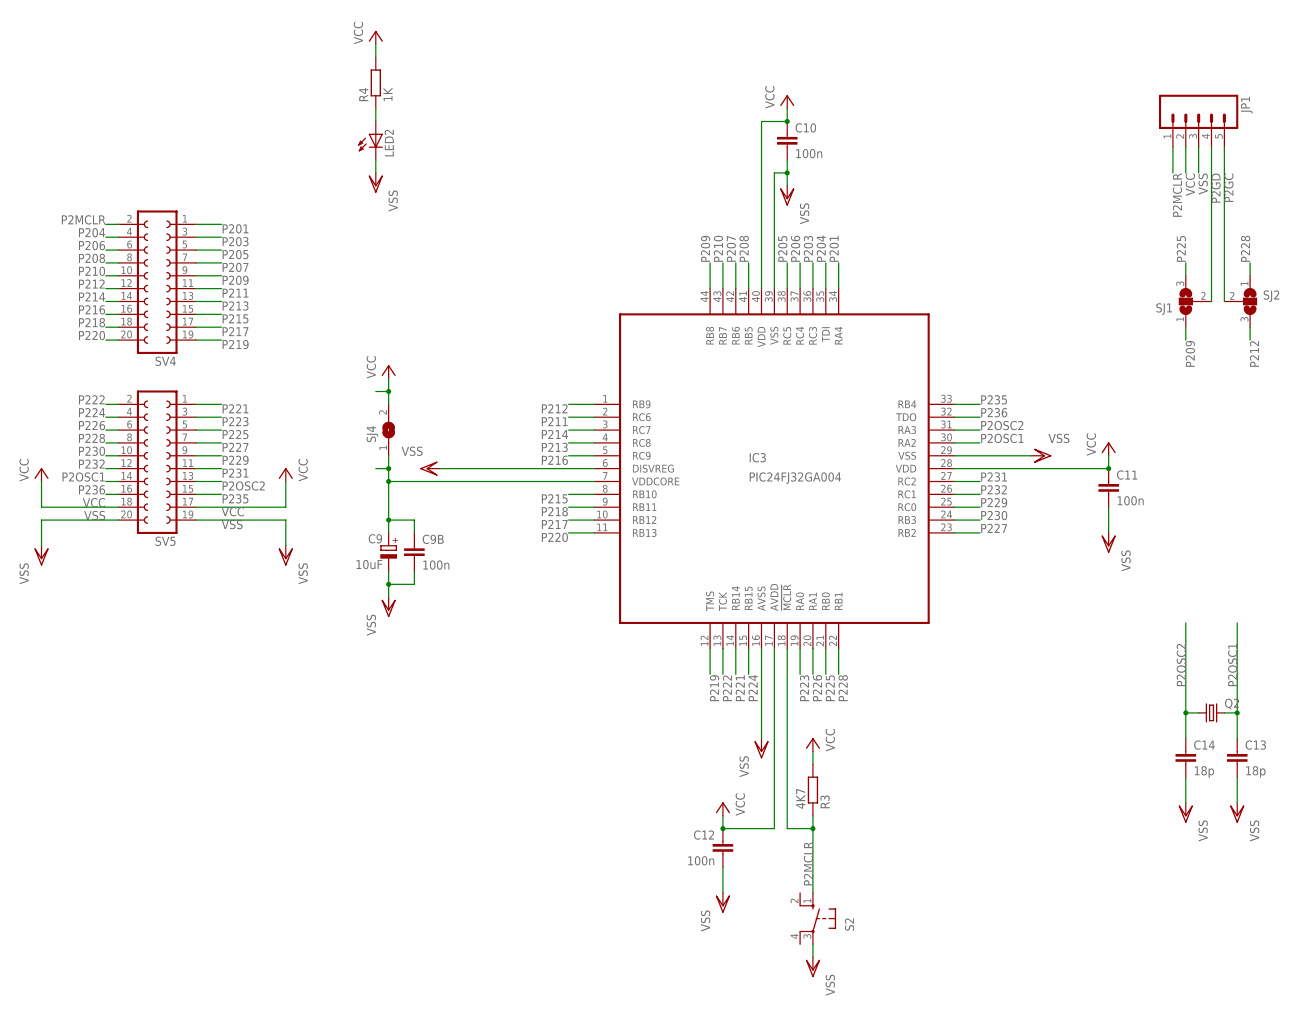
[picture p45: schematic ARE_adaptadores_final.sch, sheet 2, dsPIC / 24F / PIC32 44 pin]

Parts:
C9: 10uF; SMC_C
C9B, C10, C11, C12: 100n; C0805
C13, C14: 18p; C0805
IC3: PIC24FJ32GA004; TQFP44
JP1: M05PTH; 1X05
LED2: LEDCHIPLED_0805; CHIPLED_0805
Q2: CRYSTALHC18U-V; HC18U-V
R3: 4K7; R0805
R4: 1K; R0805
S2: 10-XX; B3F-10XX; MPN B3F-1000
SJ1, SJ2: SJ2W; SJ_2
SJ4: SJ
SV4, SV5: FE10-2W

Connections:
unnamed: LED2.A, R4.1
unnamed: C9.+, C9B.1, IC3.7 (VDDCORE), SJ4.1
P2GC: JP1.5, SJ2.2
P2GD: JP1.4, SJ1.2
P2MCLR: IC3.18 (!MCLR), JP1.1, R3.1, S2.1 (S), SV4.2
P2OSC1: C13.1, IC3.30 (RA2), Q2.2, SV5.14
P2OSC2: C14.1, IC3.31 (RA3), Q2.1, SV5.13
P201: IC3.34 (RA4), SV4.1
P203: IC3.36 (RC3), SV4.3
P204: IC3.35 (TDI), SV4.4
P205: IC3.38 (RC5), SV4.5
P206: IC3.37 (RC4), SV4.6
P207: IC3.42 (RB6), SV4.7
P208: IC3.41 (RB5), SV4.8
P209: IC3.44 (RB8), SJ1.1, SV4.9
P210: IC3.43 (RB7), SV4.10
P211: IC3.2 (RC6), SV4.11
P212: IC3.1 (RB9), SJ2.3, SV4.12
P213: IC3.4 (RC8), SV4.13
P214: IC3.3 (RC7), SV4.14
P215: IC3.8 (RB10), SV4.15
P216: IC3.5 (RC9), SV4.16
P217: IC3.10 (RB12), SV4.17
P218: IC3.9 (RB11), SV4.18
P219: IC3.12 (TMS), SV4.19
P220: IC3.11 (RB13), SV4.20
P221: IC3.14 (RB14), SV5.1
P222: IC3.13 (TCK), SV5.2
P223: IC3.19 (RA0), SV5.3
P224: IC3.15 (RB15), SV5.4
P225: IC3.21 (RB0), SJ1.3, SV5.5
P226: IC3.20 (RA1), SV5.6
P227: IC3.23 (RB2), SV5.7
P228: IC3.22 (RB1), SJ2.1, SV5.8
P229: IC3.25 (RC0), SV5.9
P230: IC3.24 (RB3), SV5.10
P231: IC3.27 (RC2), SV5.11
P232: IC3.26 (RC1), SV5.12
P235: IC3.33 (RB4), SV5.15
P236: IC3.32 (TDO), SV5.16
VCC: C10.1, C11.1, C12.1, IC3.17 (AVDD), IC3.28 (VDD), IC3.40 (VDD), JP1.2, R3.2, R4.2, SJ4.2, SV5.17, SV5.18; also elsewhere on the board
VSS: C9.-, C9B.2, C10.2, C11.2, C12.2, C13.2, C14.2, IC3.6 (DISVREG), IC3.16 (AVSS), IC3.29 (VSS), IC3.39 (VSS), JP1.3, LED2.C, S2.3, SV5.19, SV5.20; also elsewhere on the board
