dragonet80/MultiMicro/Adaptadores/ARE_adaptadores_final.brd

## EAGLE design Adaptadores/_OLD_/ARE_adaptadores_final.brd (continued)

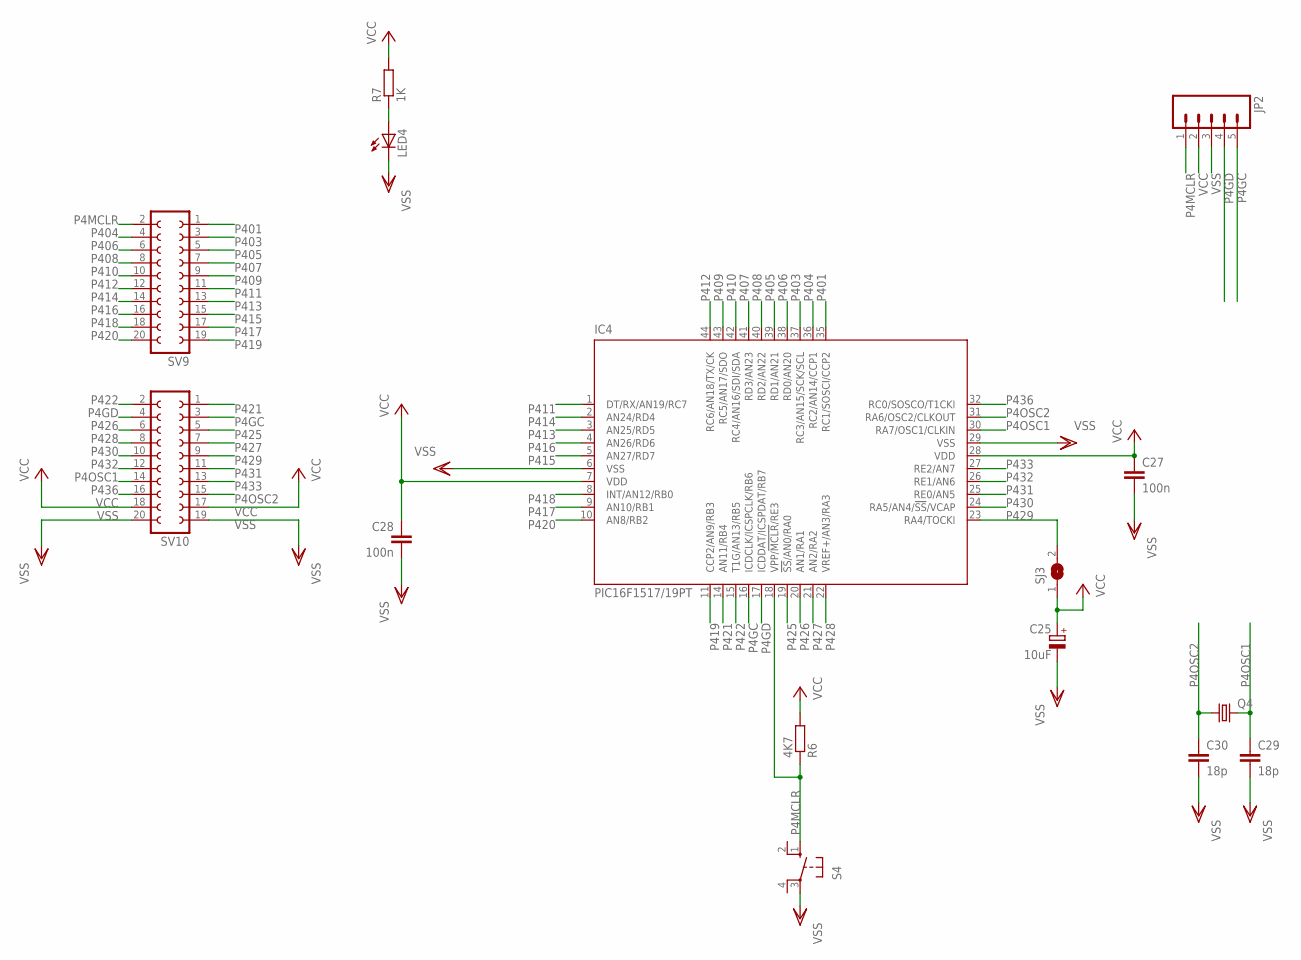
[picture p46: schematic ARE_adaptadores_final.sch, sheet 3, PIC 16F / 18F 44 pin]

Parts:
C25: 10uF; SMC_C
C27, C28: 100n; C0805
C29, C30: 18p; C0805
IC4: PIC16F1517/19PT; TQFP44
JP2: M05PTH; 1X05
LED4: LEDCHIPLED_0805; CHIPLED_0805
Q4: CRYSTALHC18U-V; HC18U-V
R6: 4K7; R0805
R7: 1K; R0805
S4: 10-XX; B3F-10XX; MPN B3F-1000
SJ3: SJ
SV9, SV10: FE10-2W

Connections:
unnamed: LED4.A, R7.1
P4GC: IC4.16 (ICDCLK/ICSPCLK/RB6), JP2.5, SV10.3
P4GD: IC4.17 (ICDDAT/ICSPDAT/RB7), JP2.4, SV10.4
P4MCLR: IC4.18 (VPP/!MCLR!/RE3), JP2.1, R6.1, S4.1 (S), SV9.2
P4OSC1: C29.1, IC4.30 (RA7/OSC1/CLKIN), Q4.2, SV10.14
P4OSC2: C30.1, IC4.31 (RA6/OSC2/CLKOUT), Q4.1, SV10.15
P401: IC4.35 (RC1/SOSCI/CCP2), SV9.1
P403: IC4.37 (RC3/AN15/SCK/SCL), SV9.3
P404: IC4.36 (RC2/AN14/CCP1), SV9.4
P405: IC4.39 (RD1/AN21), SV9.5
P406: IC4.38 (RD0/AN20), SV9.6
P407: IC4.41 (RD3/AN23), SV9.7
P408: IC4.40 (RD2/AN22), SV9.8
P409: IC4.43 (RC5/AN17/SDO), SV9.9
P410: IC4.42 (RC4/AN16/SDI/SDA), SV9.10
P411: IC4.1 (DT/RX/AN19/RC7), SV9.11
P412: IC4.44 (RC6/AN18/TX/CK), SV9.12
P413: IC4.3 (AN25/RD5), SV9.13
P414: IC4.2 (AN24/RD4), SV9.14
P415: IC4.5 (AN27/RD7), SV9.15
P416: IC4.4 (AN26/RD6), SV9.16
P417: IC4.9 (AN10/RB1), SV9.17
P418: IC4.8 (INT/AN12/RB0), SV9.18
P419: IC4.11 (CCP2/AN9/RB3), SV9.19
P420: IC4.10 (AN8/RB2), SV9.20
P421: IC4.14 (AN11/RB4), SV10.1
P422: IC4.15 (T1G/AN13/RB5), SV10.2
P425: IC4.19 (!SS!/AN0/RA0), SV10.5
P426: IC4.20 (AN1/RA1), SV10.6
P427: IC4.21 (AN2/RA2), SV10.7
P428: IC4.22 (VREF+/AN3/RA3), SV10.8
P429: IC4.23 (RA4/TOCKI), SJ3.2, SV10.9
P430: IC4.24 (RA5/AN4/!SS!/VCAP), SV10.10
P431: IC4.25 (RE0/AN5), SV10.11
P432: IC4.26 (RE1/AN6), SV10.12
P433: IC4.27 (RE2/AN7), SV10.13
P436: IC4.32 (RC0/SOSCO/T1CKI), SV10.16
VCC: C25.+, C27.1, C28.1, IC4.7 (VDD), IC4.28 (VDD), JP2.2, R6.2, R7.2, SJ3.1, SV10.17, SV10.18; also elsewhere on the board
VSS: C25.-, C27.2, C28.2, C29.2, C30.2, IC4.6 (VSS), IC4.29 (VSS), JP2.3, LED4.C, S4.3, SV10.19, SV10.20; also elsewhere on the board


Parts:
C32, C35, C36: 100n; C0805
C33, C34: 18p; C0805
IC2: 12F; SOCKET-08
IC5: 16F; SOCKET-14
IC6: 10F; SOCKET-08
JP3: M05PTH; 1X05
LED5: LEDCHIPLED_0805; CHIPLED_0805
Q6: CRYSTALHC18U-V; HC18U-V
R8: 4K7; R0805
R9: 1K; R0805
S5: 10-XX; B3F-10XX; MPN B3F-1000
SV11, SV12: FE10-2W

Connections:
unnamed: LED5.A, R9.1
P5GC: IC2.6, IC5.12, IC6.4, JP3.5, SV11.5, SV11.11, SV12.9
P5GD: IC2.7, IC5.13, IC6.5, JP3.4, SV11.3, SV11.12, SV12.11
P5MCLR: IC2.4, IC5.4, IC6.8, JP3.1, R8.1, S5.1 (S), SV11.1, SV11.15, SV12.8
P5OSC1: C33.1, IC5.2, Q6.2, SV12.12
P5OSC2: C34.1, IC5.3, Q6.1, SV12.10
P502: SV11.2
P504: SV11.4
P506: SV11.6
P507: IC6.3, SV11.7
P508: SV11.8
P513: IC2.5, SV11.13
P514: SV11.14
P516: SV11.16
P517: IC2.3, SV11.17
P518: IC2.2, SV11.18
P521: IC5.8, SV12.1
P522: IC5.7, SV12.2
P523: IC5.9, SV12.3
P524: IC5.6, SV12.4
P525: IC5.10, SV12.5
P526: IC5.5, SV12.6
P527: IC5.11, SV12.7
P533: SV12.13
P534: SV12.14
P535: SV12.15
P536: SV12.16
VCC: C32.1, C35.1, C36.1, IC2.1, IC5.1, IC6.2, JP3.2, R8.2, R9.2, SV11.9, SV11.10, SV11.19, SV11.20, SV12.17, SV12.18; also elsewhere on the board
VSS: C32.2, C33.2, C34.2, C35.2, C36.2, IC2.8, IC5.14, IC6.7, JP3.3, LED5.C, S5.3, SV12.19, SV12.20; also elsewhere on the board

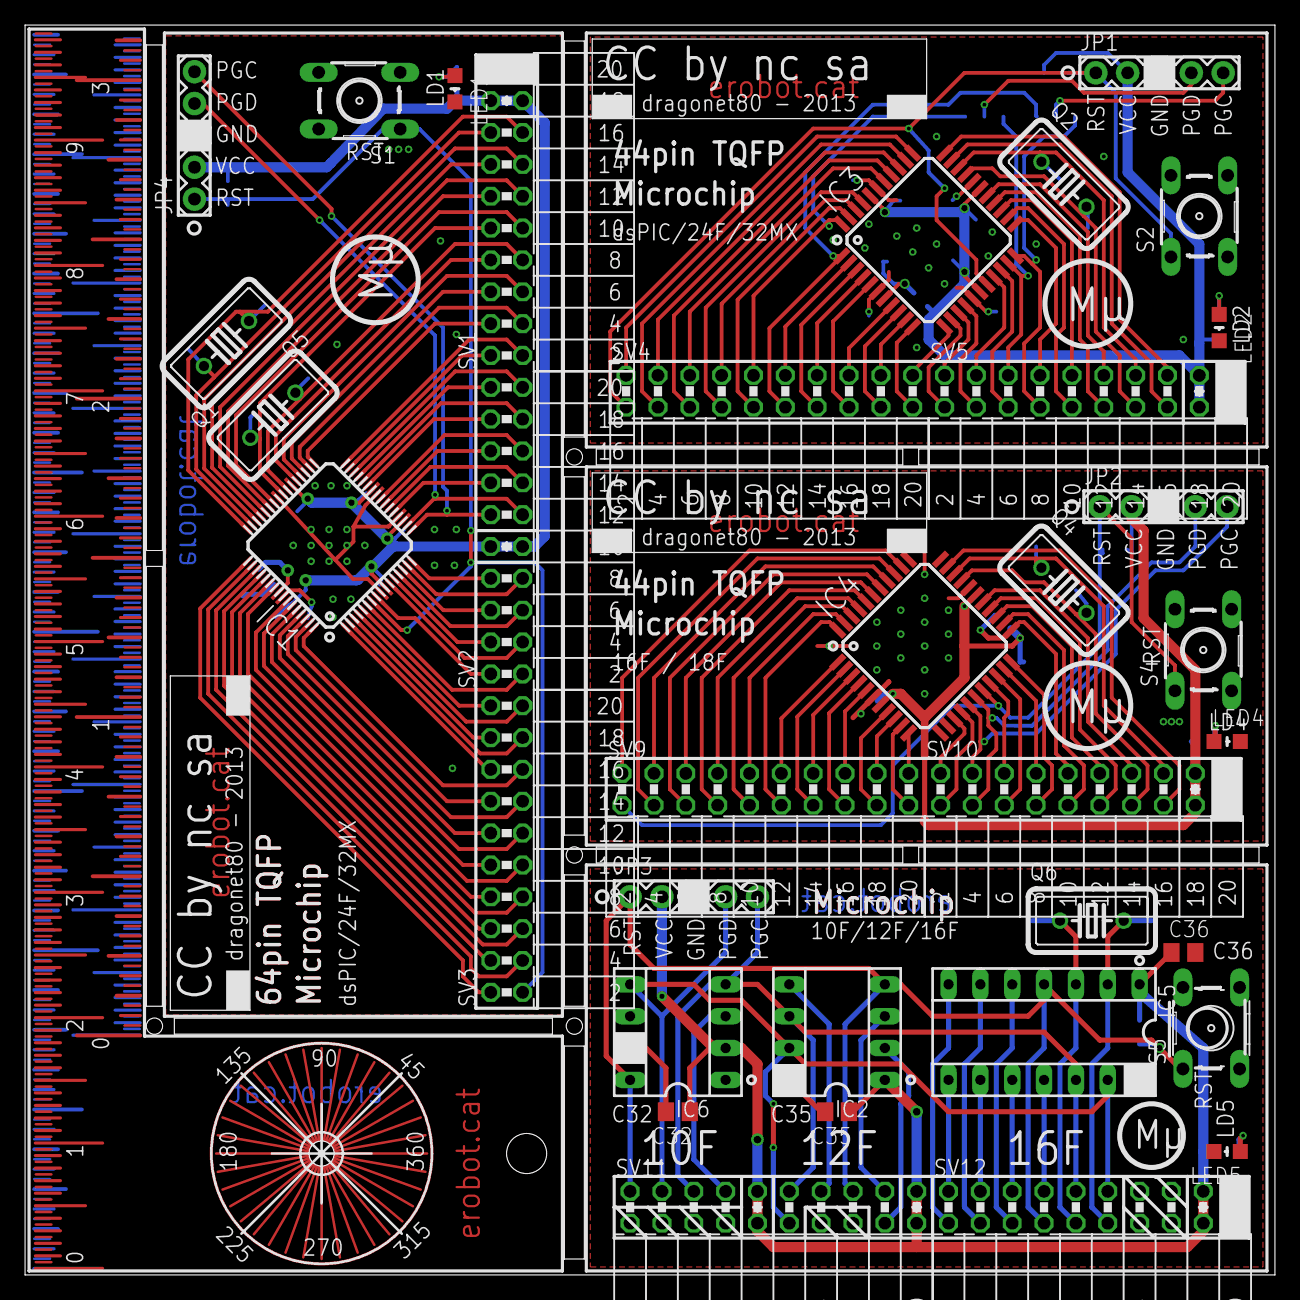
[picture p47: board ARE_adaptadores_final.brd from above]

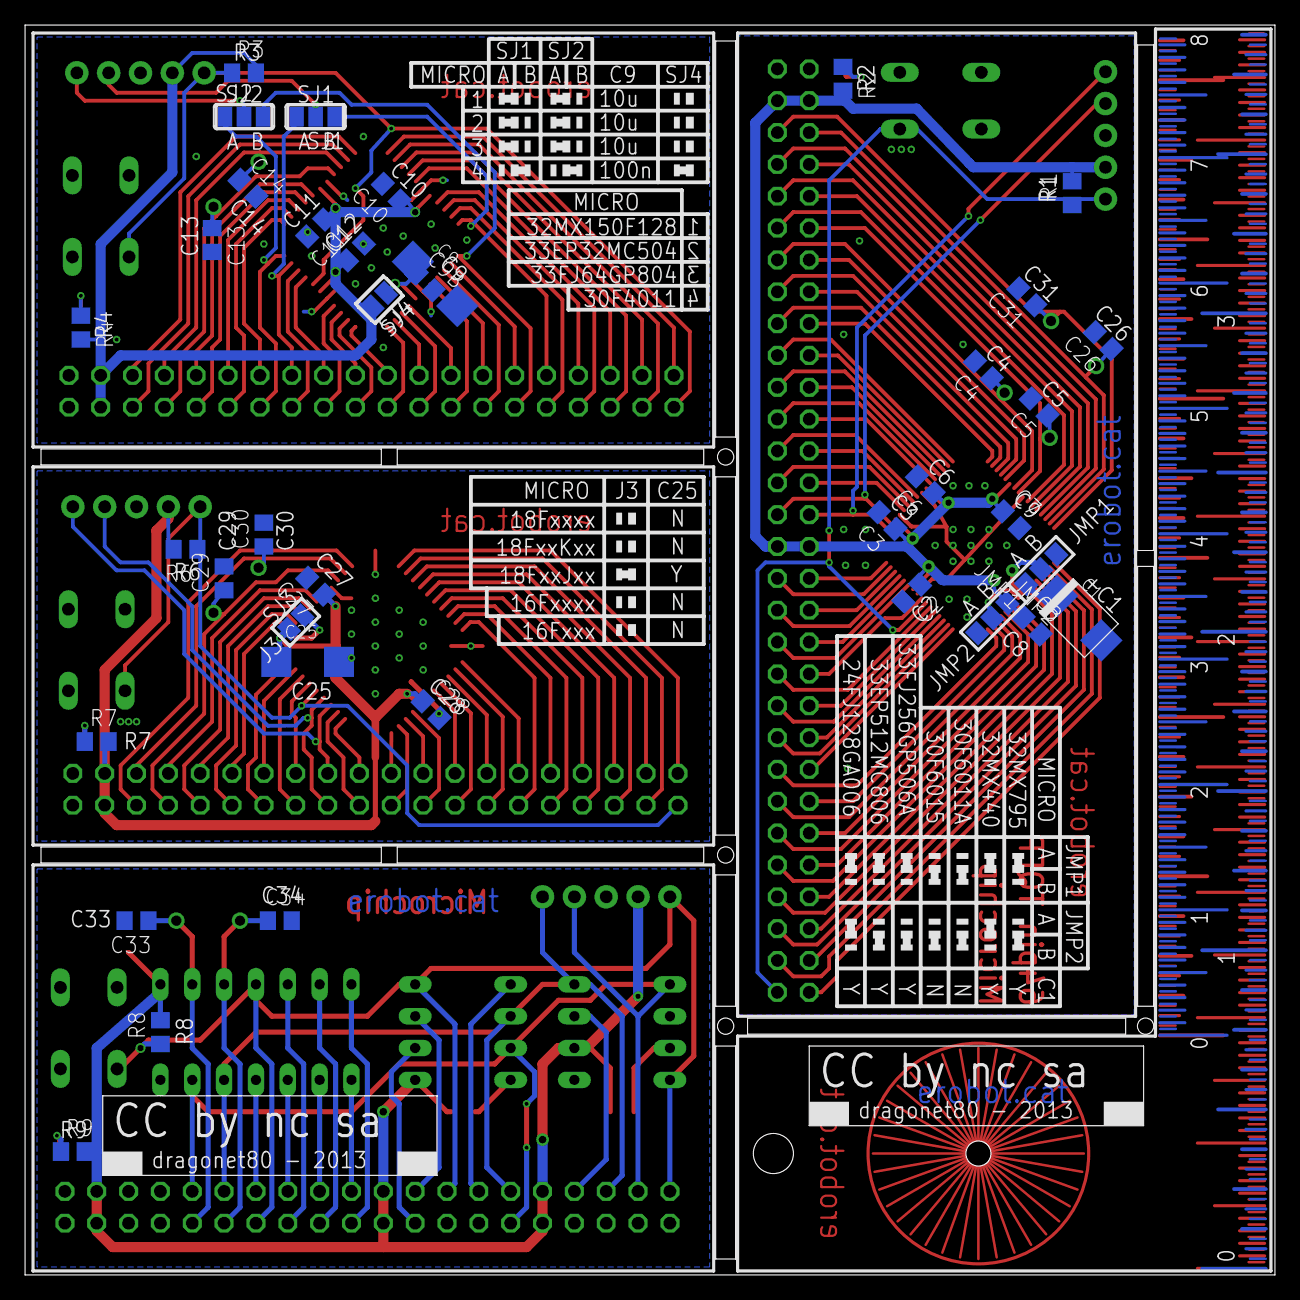
[picture p48: board ARE_adaptadores_final.brd from below]

Board: 2 copper layers, 99.7 x 99.7 mm, 73 parts (38 on the bottom side), 154 nets.
