dragonet80/MultiMicro/Base/_OLD_/multiMicro_base_64pin.brd

## EAGLE design Base/_OLD_/multiMicro_base_64pin.brd (2013-05-07, an earlier design)

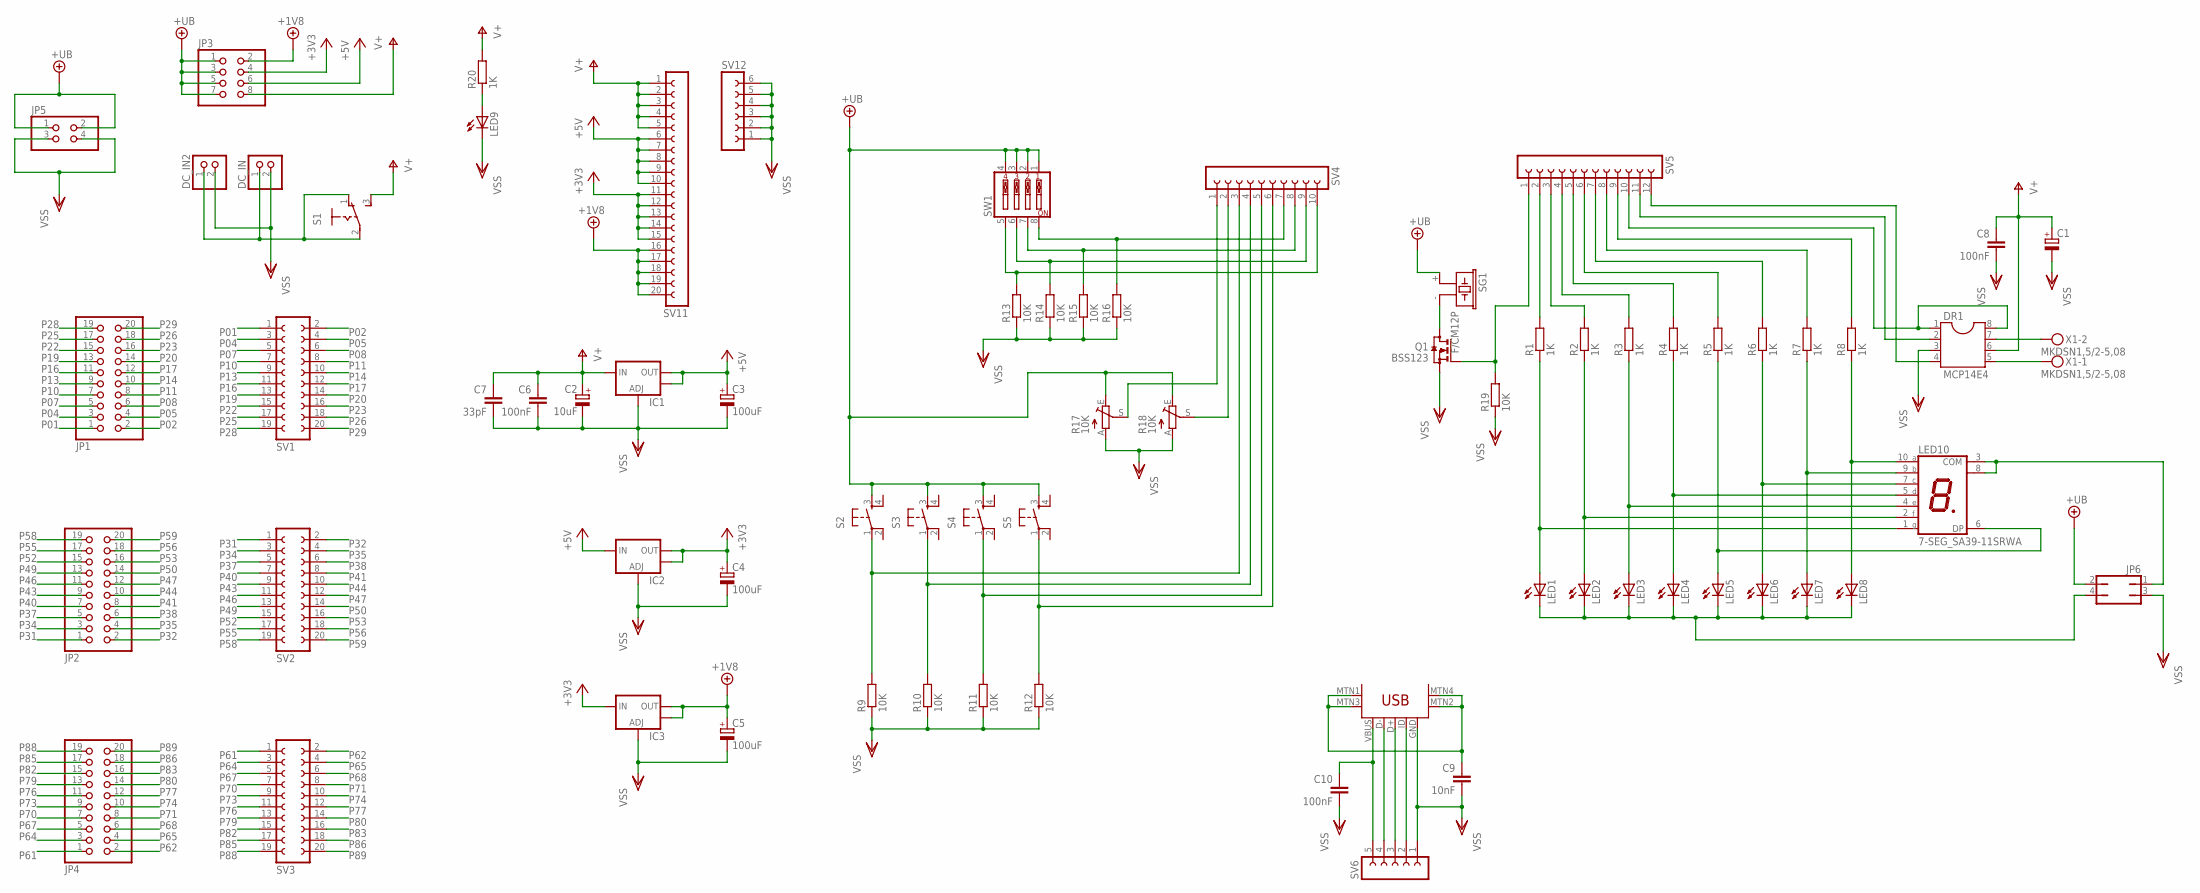
[picture p49: schematic multiMicro_base_64pin.sch]

Parts:
C1: CPOL-EU140CLH-0810; 140CLH-0810
C2: 10uF; SMC_C
C3, C4, C5: 100uF; CT7343
C6, C8, C10: 100nF; C0805
C7: 33pF; C0805
C9: 10nF; C0805
DC_IN, DC_IN2: PINHD-1X2/90; 1X02/90
DR1: MCP14E4; SOIC08
IC1, IC2, IC3: V_REG_LM1117SOT223; SOT223
JP1, JP2, JP4: PINHD-2X10/90; 2X10/90
JP3: PINHD-2X4; 2X04
JP5: PINHD-2X2/90; 2X02/90
JP6: JP2Q
LED1, LED2, LED3, LED4, LED5, LED6, LED7, LED8, LED9: LEDCHIP-LED0805; CHIP-LED0805
LED10: 7-SEG_SA39-11SRWA; SA39-11SRWA
Q1: BSS123; SOT23
R1, R2, R3, R4, R5, R6, R7, R8, R20: 1K; R0805
R9, R10, R11, R12, R13, R14, R15, R16, R19: 10K; R0805
R17, R18: 10K; CA6V
S1: 255SB
S2, S3, S4, S5: TAC_SWITCHPTH; TACTILE-PTH
SG1: F/CM12P
SV1, SV2, SV3: FE10-2
SV4: FE10-1; FE10
SV5: FE12-1; FE12
SV6: FE05-1
SV11: FE20-1; FE20
SV12: FE06-1; FE06
SW1: SW_DIP-4; EDG-04
U$1: USB-MINIB-5PIN; USB-MINIB
X1: MKDSN1,5/2-5,08

Connections:
+3V3: C4.+, IC2.2 (OUT), IC2.4 (OUT), IC3.3 (IN), JP3.4, SV11.11, SV11.12, SV11.13, SV11.14, SV11.15
+5V: C3.+, IC1.2 (OUT), IC1.4 (OUT), IC2.3 (IN), JP3.6, SV11.6, SV11.7, SV11.8, SV11.9, SV11.10
+18V: C5.+, IC3.2 (OUT), IC3.4 (OUT), JP3.2, SV11.16, SV11.17, SV11.18, SV11.19, SV11.20
+UB: JP3.1, JP3.3, JP3.5, JP3.7, JP5.1, JP5.2, JP6.2, R17.E, R18.E, S2.3, S3.3, S4.3, S5.3, SG1.+ (1), SW1.1, SW1.2, SW1.3, SW1.4
unnamed: LED1.A, LED10.1 (G), R1.1
unnamed: LED2.A, LED10.2 (F), R2.1
unnamed: LED3.A, LED10.4 (E), R3.1
unnamed: LED4.A, LED10.5 (D), R4.1
unnamed: R2.2, SV5.3
unnamed: R3.2, SV5.4
unnamed: R1.2, SV5.2
unnamed: R4.2, SV5.5
unnamed: LED9.A, R20.1
unnamed: R18.S, SV4.2
unnamed: DR1.5, X1.1
unnamed: DR1.7, X1.2
unnamed: DR1.2, SV5.11
unnamed: DR1.4, SV5.12
unnamed: DR1.1, DR1.8, SV5.10
unnamed: JP6.4, LED1.C, LED2.C, LED3.C, LED4.C, LED5.C, LED6.C, LED7.C, LED8.C
unnamed: JP6.1, LED10.3 (COM), LED10.8 (COM)
unnamed: Q1.3 (D), SG1.- (2)
unnamed: SV6.2, U$1.ID
unnamed: LED5.A, LED10.6 (DP), R5.1
unnamed: C9.1, U$1.MTN1 (MTN2), U$1.MTN2 (MTN3), U$1.MTN3 (MTN1), U$1.MTN4
unnamed: SV6.3, U$1.D+
unnamed: SV6.4, U$1.D-
unnamed: C10.1, SV6.5, U$1.VBUS
unnamed: DC_IN.1, DC_IN2.1, S1.1 (O), S1.2
unnamed: LED6.A, LED10.7 (C), R6.1
unnamed: LED7.A, LED10.9 (B), R7.1
unnamed: LED8.A, LED10.10 (A), R8.1
unnamed: R9.2, S2.1, SV4.3
unnamed: R10.2, S3.1, SV4.4
unnamed: R11.2, S4.1, SV4.5
unnamed: R12.2, S5.1, SV4.6
unnamed: Q1.1 (G), R19.2, SV5.1
unnamed: R17.S, SV4.1
unnamed: R6.2, SV5.7
unnamed: R7.2, SV5.8
unnamed: R5.2, SV5.6
unnamed: R8.2, SV5.9
unnamed: R13.2, SV4.10, SW1.5
unnamed: R14.2, SV4.9, SW1.6
unnamed: R15.2, SV4.8, SW1.7
unnamed: R16.2, SV4.7, SW1.8
P01: JP1.1, SV1.1
P02: JP1.2, SV1.2
P04: JP1.3, SV1.3
P05: JP1.4, SV1.4
P07: JP1.5, SV1.5
P08: JP1.6, SV1.6
P10: JP1.7, SV1.7
P11: JP1.8, SV1.8
P13: JP1.9, SV1.9
P14: JP1.10, SV1.10
P16: JP1.11, SV1.11
P17: JP1.12, SV1.12
P19: JP1.13, SV1.13
P20: JP1.14, SV1.14
P22: JP1.15, SV1.15
P23: JP1.16, SV1.16
P25: JP1.17, SV1.17
P26: JP1.18, SV1.18
P28: JP1.19, SV1.19
P29: JP1.20, SV1.20
P31: JP2.1, SV2.1
P32: JP2.2, SV2.2
P34: JP2.3, SV2.3
P35: JP2.4, SV2.4
P37: JP2.5, SV2.5
P38: JP2.6, SV2.6
P40: JP2.7, SV2.7
P41: JP2.8, SV2.8
P43: JP2.9, SV2.9
P44: JP2.10, SV2.10
P46: JP2.11, SV2.11
P47: JP2.12, SV2.12
P49: JP2.13, SV2.13
P50: JP2.14, SV2.14
P52: JP2.15, SV2.15
P53: JP2.16, SV2.16
P55: JP2.17, SV2.17
P56: JP2.18, SV2.18
P58: JP2.19, SV2.19
P59: JP2.20, SV2.20
P61: JP4.1, SV3.1
P62: JP4.2, SV3.2
P64: JP4.3, SV3.3
P65: JP4.4, SV3.4
P67: JP4.5, SV3.5
P68: JP4.6, SV3.6
P70: JP4.7, SV3.7
P71: JP4.8, SV3.8
P73: JP4.9, SV3.9
P74: JP4.10, SV3.10
P76: JP4.11, SV3.11
P77: JP4.12, SV3.12
P79: JP4.13, SV3.13
P80: JP4.14, SV3.14
P82: JP4.15, SV3.15
P83: JP4.16, SV3.16
P85: JP4.17, SV3.17
P86: JP4.18, SV3.18
P88: JP4.19, SV3.19
P89: JP4.20, SV3.20
V+: C1.+, C2.+, C6.1, C7.1, C8.1, DR1.6, IC1.3 (IN), JP3.8, R20.2, S1.3 (S), SV11.1, SV11.2, SV11.3, SV11.4, SV11.5
VSS: C1.-, C2.-, C3.-, C4.-, C5.-, C6.2, C7.2, C8.2, C9.2, C10.2, DC_IN.2, DC_IN2.2, DR1.3, IC1.1 (ADJ), IC2.1 (ADJ), IC3.1 (ADJ), JP5.3, JP5.4, JP6.3, LED9.C, Q1.2 (S), R9.1, R10.1, R11.1, R12.1, R13.1, R14.1, R15.1, R16.1, R17.A, R18.A, R19.1, SV6.1, SV12.1, SV12.2, SV12.3, SV12.4, SV12.5, SV12.6, U$1.GND

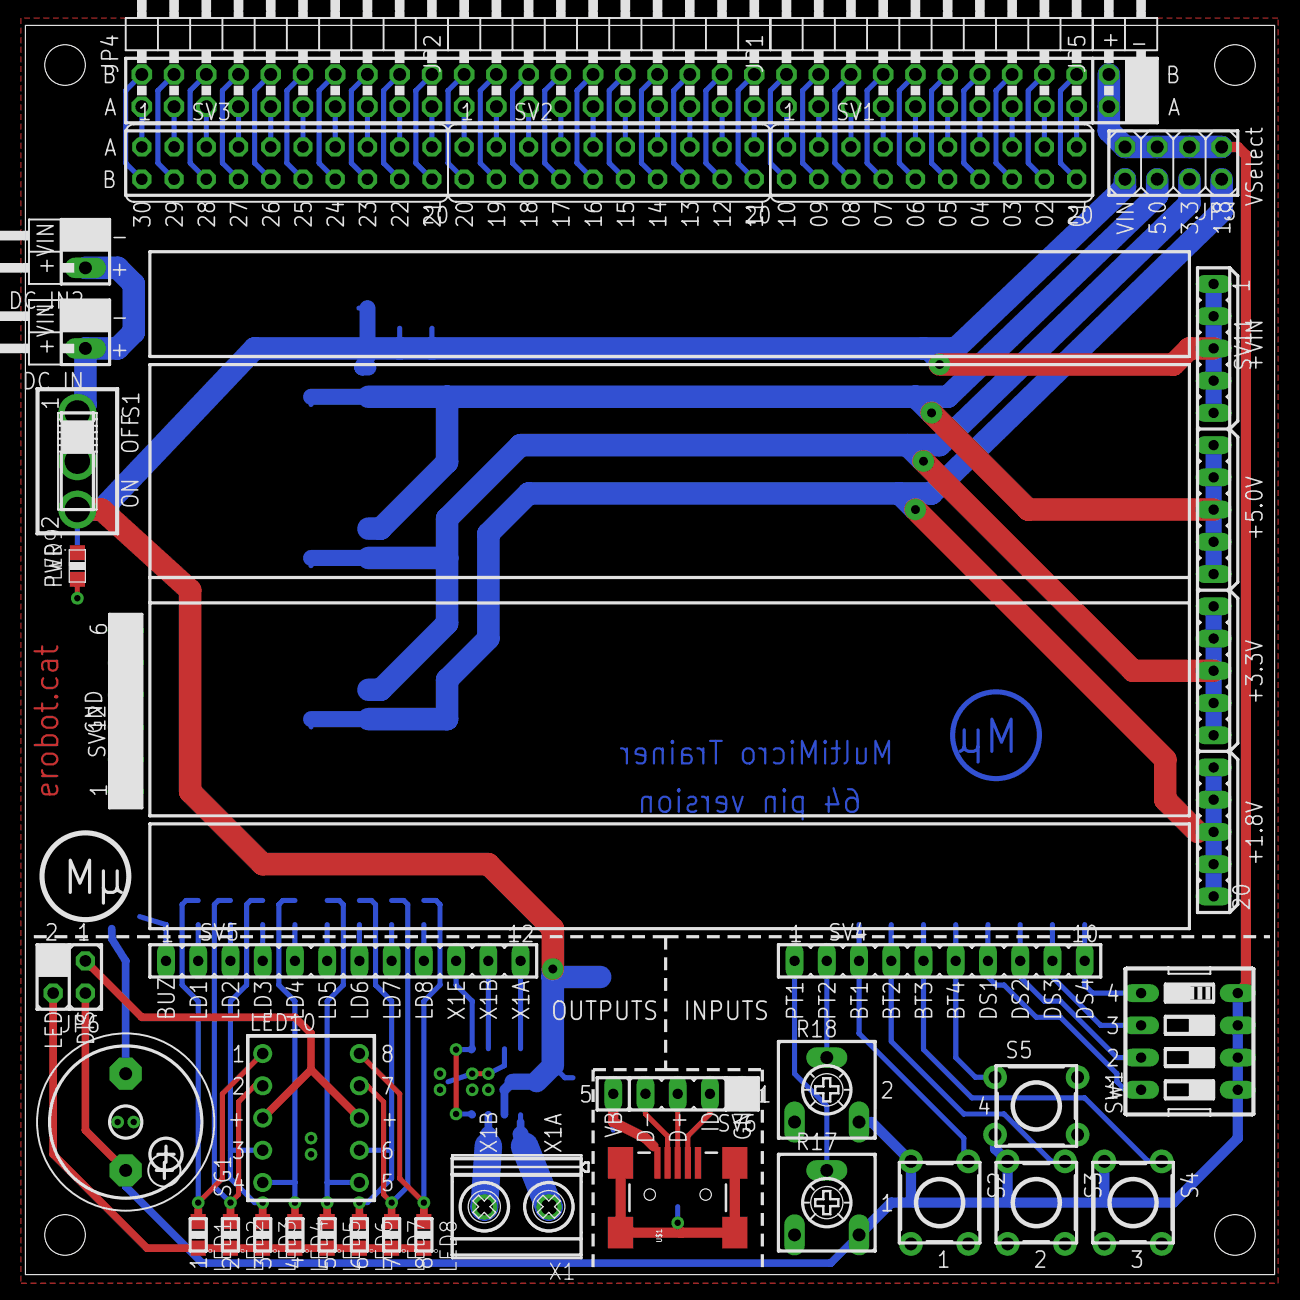
[picture p50: board multiMicro_base_64pin.brd from above]

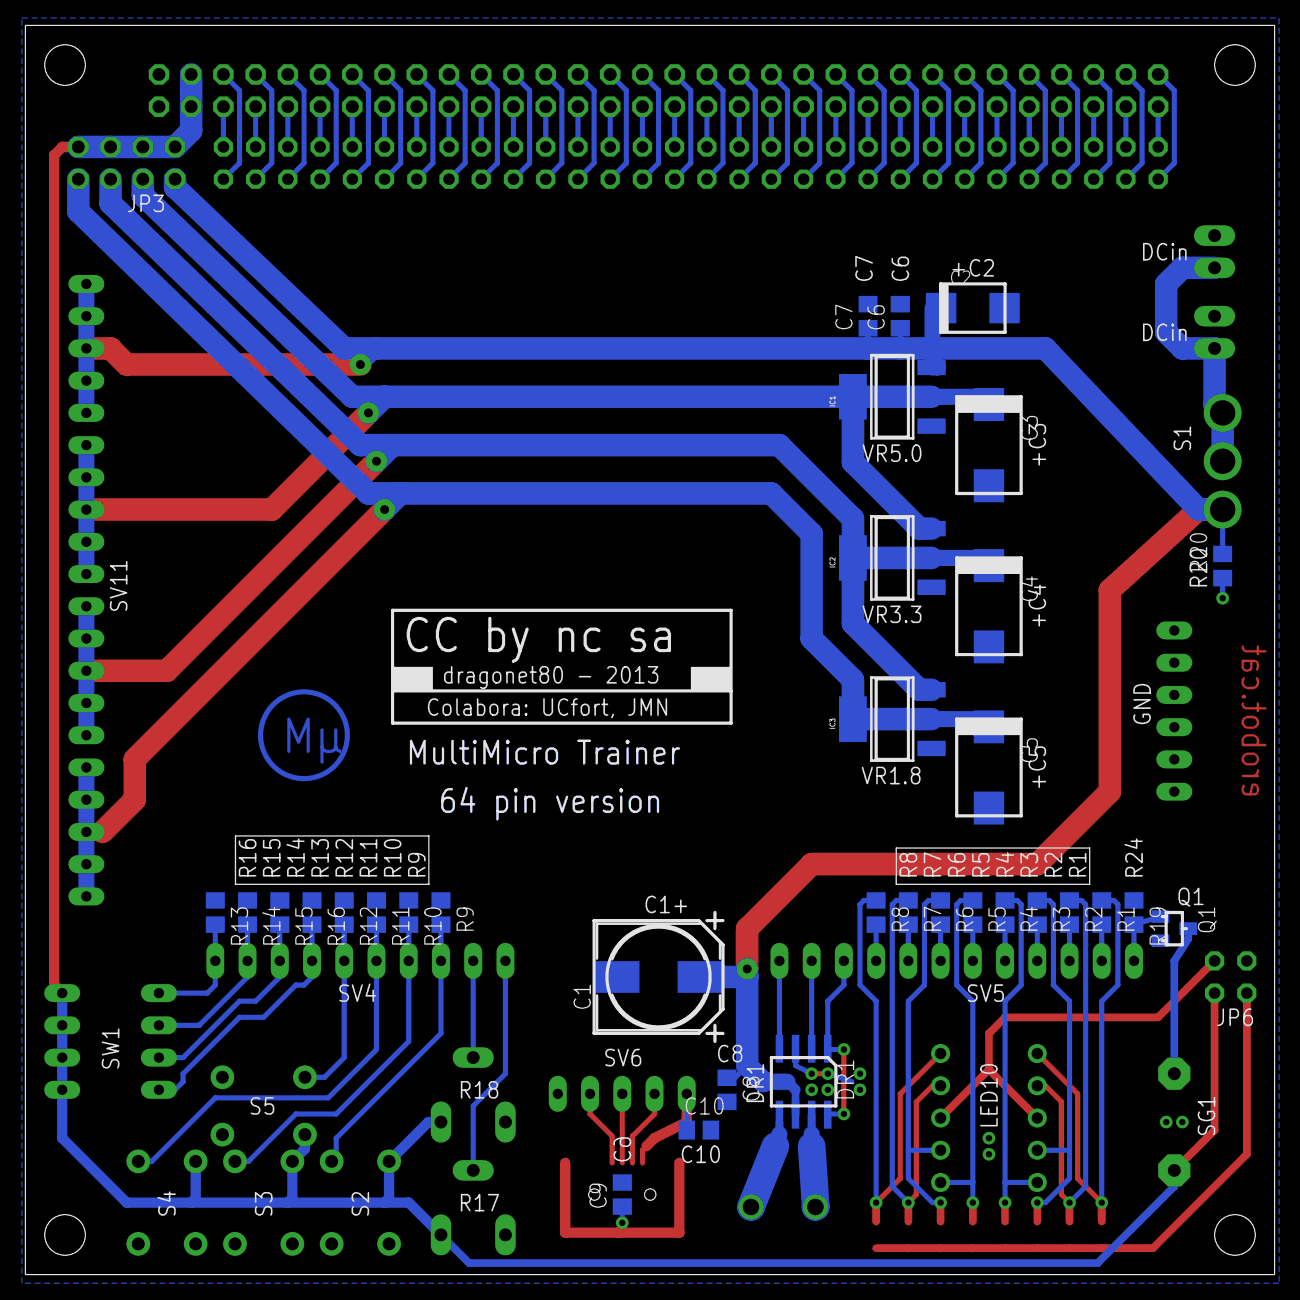
[picture p51: board multiMicro_base_64pin.brd from below]

Board: 2 copper layers, 98.4 x 98.4 mm, 70 parts (33 on the bottom side), 108 nets.
