dragonet80/MultiMicro/Adaptadores/Microchip/ARE_adaptadora_PIC_40pin.brd

## EAGLE design Adaptadores/Microchip/ARE_adaptadora_PIC_40pin.brd (2015-02-18)

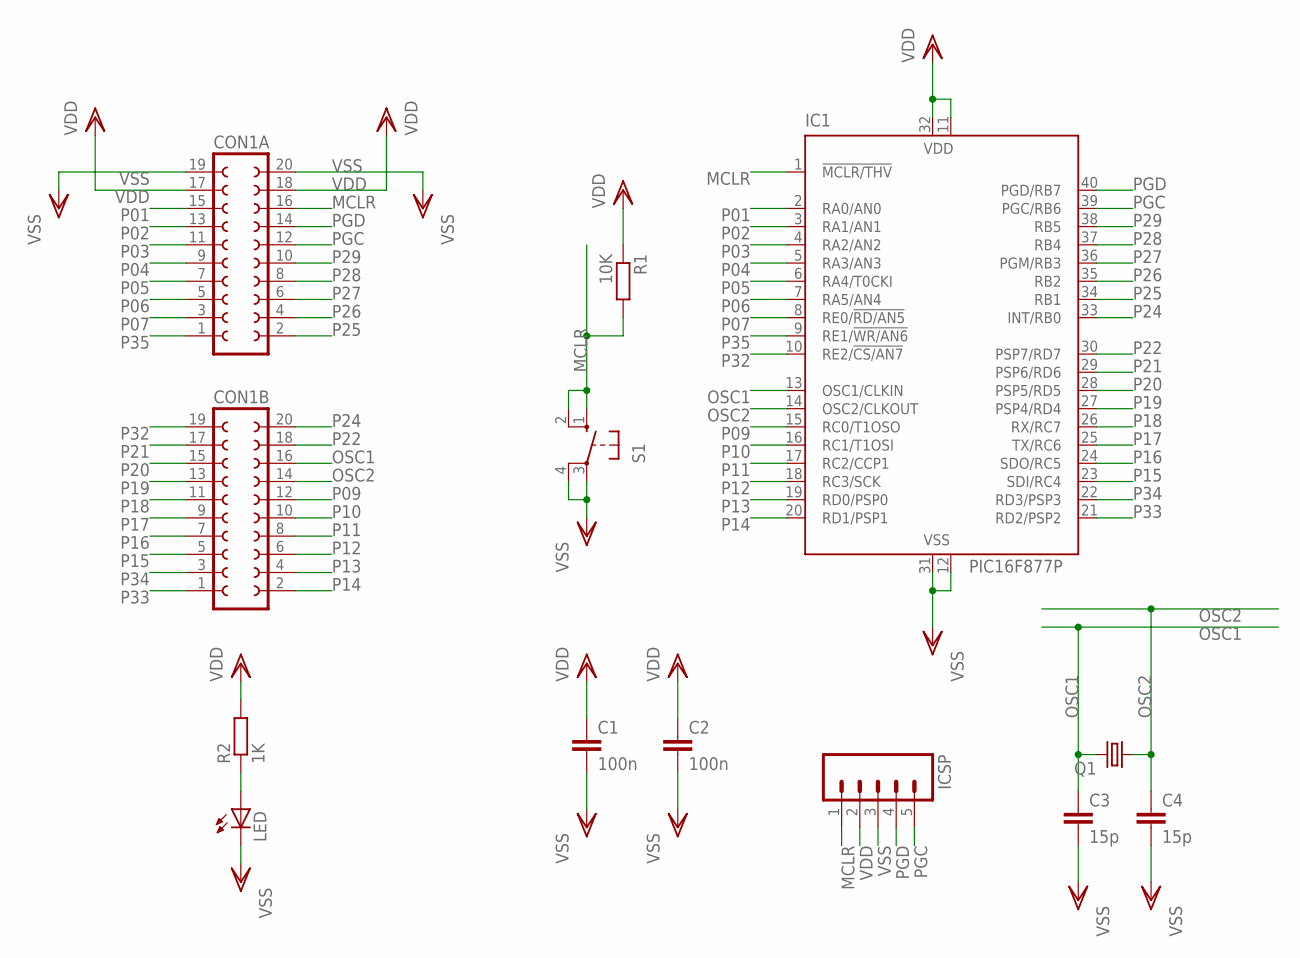
[picture p52: schematic ARE_adaptadora_PIC_40pin.sch, 16F/18F 40 pin DIP]

Parts:
C1, C2: 100n; C0805
C3, C4: 15p; C0805
CON1A, CON1B: FE10-2W
IC1: PIC16F877P; DIL40
ICSP: M05PTH; 1X05
LED: LED3MM
Q1: CRYSTALHC18U-V; HC18U-V
R1: 10K; R0805
R2: 1K; R0805
S1: 10-XX; B3F-10XX; MPN B3F-1000

Connections:
MCLR: CON1A.16, IC1.1 (!MCLR/THV), ICSP.1, R1.2, S1.1 (S), S1.2 (S1)
unnamed: LED.A, R2.1
OSC1: C3.1, CON1B.16, IC1.13 (OSC1/CLKIN), Q1.2
OSC2: C4.1, CON1B.14, IC1.14 (OSC2/CLKOUT), Q1.1
P01: CON1A.15, IC1.2 (RA0/AN0)
P02: CON1A.13, IC1.3 (RA1/AN1)
P03: CON1A.11, IC1.4 (RA2/AN2)
P04: CON1A.9, IC1.5 (RA3/AN3)
P05: CON1A.7, IC1.6 (RA4/T0CKI)
P06: CON1A.5, IC1.7 (RA5/AN4)
P07: CON1A.3, IC1.8 (RE0/!RD/AN5)
P09: CON1B.12, IC1.15 (RC0/T1OSO)
P10: CON1B.10, IC1.16 (RC1/T1OSI)
P11: CON1B.8, IC1.17 (RC2/CCP1)
P12: CON1B.6, IC1.18 (RC3/SCK)
P13: CON1B.4, IC1.19 (RD0/PSP0)
P14: CON1B.2, IC1.20 (RD1/PSP1)
P15: CON1B.5, IC1.23 (SDI/RC4)
P16: CON1B.7, IC1.24 (SDO/RC5)
P17: CON1B.9, IC1.25 (TX/RC6)
P18: CON1B.11, IC1.26 (RX/RC7)
P19: CON1B.13, IC1.27 (PSP4/RD4)
P20: CON1B.15, IC1.28 (PSP5/RD5)
P21: CON1B.17, IC1.29 (PSP6/RD6)
P22: CON1B.18, IC1.30 (PSP7/RD7)
P24: CON1B.20, IC1.33 (INT/RB0)
P25: CON1A.2, IC1.34 (RB1)
P26: CON1A.4, IC1.35 (RB2)
P27: CON1A.6, IC1.36 (PGM/RB3)
P28: CON1A.8, IC1.37 (RB4)
P29: CON1A.10, IC1.38 (RB5)
P32: CON1B.19, IC1.10 (RE2/!CS/AN7)
P33: CON1B.1, IC1.21 (RD2/PSP2)
P34: CON1B.3, IC1.22 (RD3/PSP3)
P35: CON1A.1, IC1.9 (RE1/!WR/AN6)
PGC: CON1A.12, IC1.39 (PGC/RB6), ICSP.5
PGD: CON1A.14, IC1.40 (PGD/RB7), ICSP.4
VDD: C1.1, C2.1, CON1A.17, CON1A.18, IC1.11 (VDD), IC1.32 (VDD), ICSP.2, R1.1, R2.2
VSS: C1.2, C2.2, C3.2, C4.2, CON1A.19, CON1A.20, IC1.12 (VSS), IC1.31 (VSS), ICSP.3, LED.K (C), S1.3, S1.4 (P1)

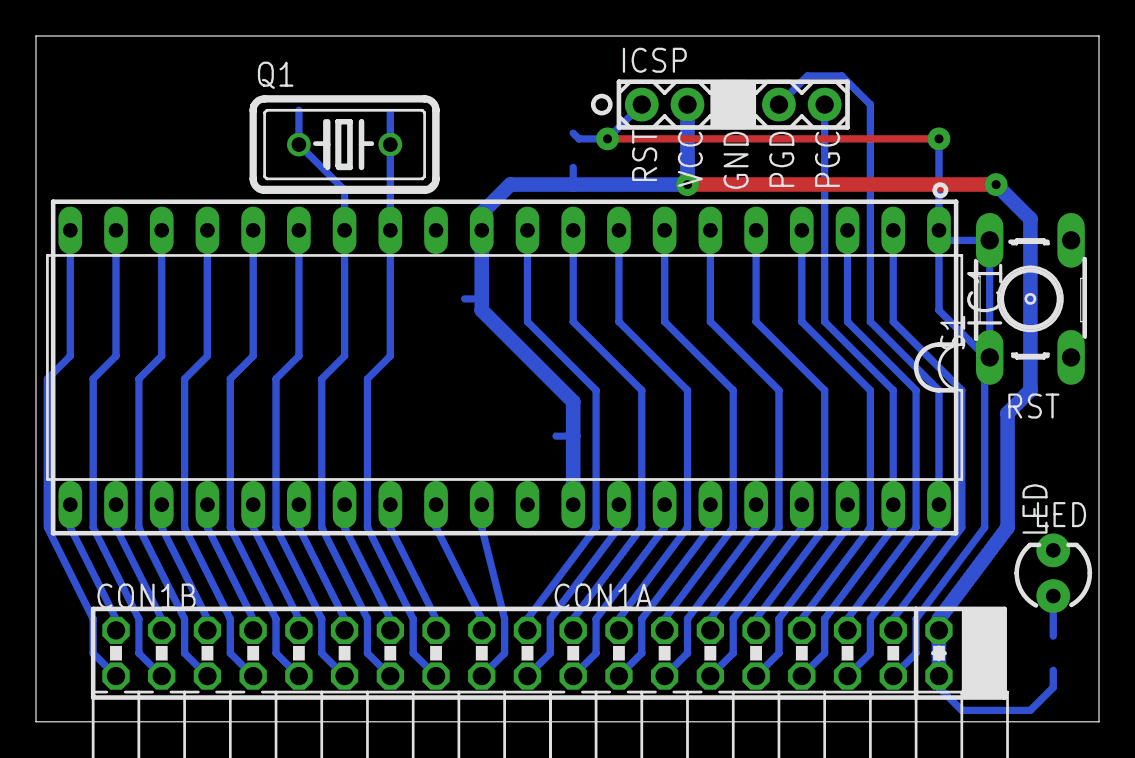
[picture p53: board ARE_adaptadora_PIC_40pin.brd from above]

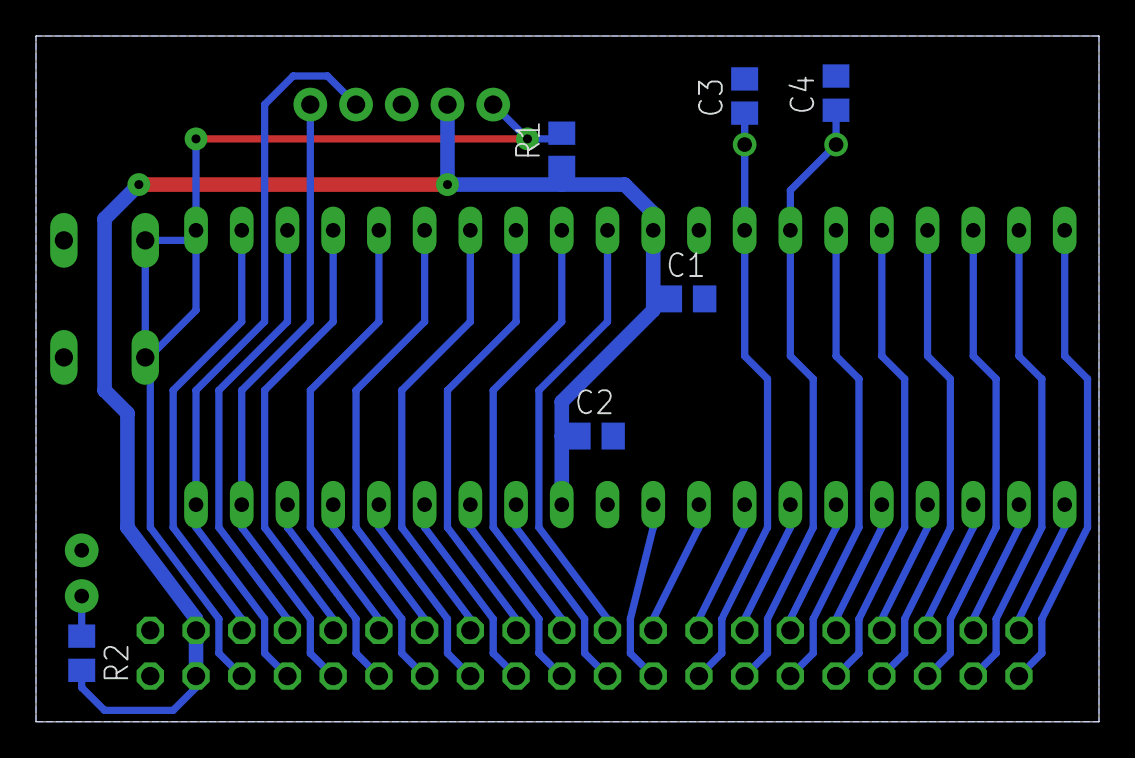
[picture p54: board ARE_adaptadora_PIC_40pin.brd from below]

Board: 2 copper layers, 59.1 x 38.1 mm, 13 parts (6 on the bottom side), 39 nets.
