dragonet80/MultiMicro/Moduls/ARE_moduls.brd

## EAGLE design Moduls/ARE_moduls.brd (2013-03-08)

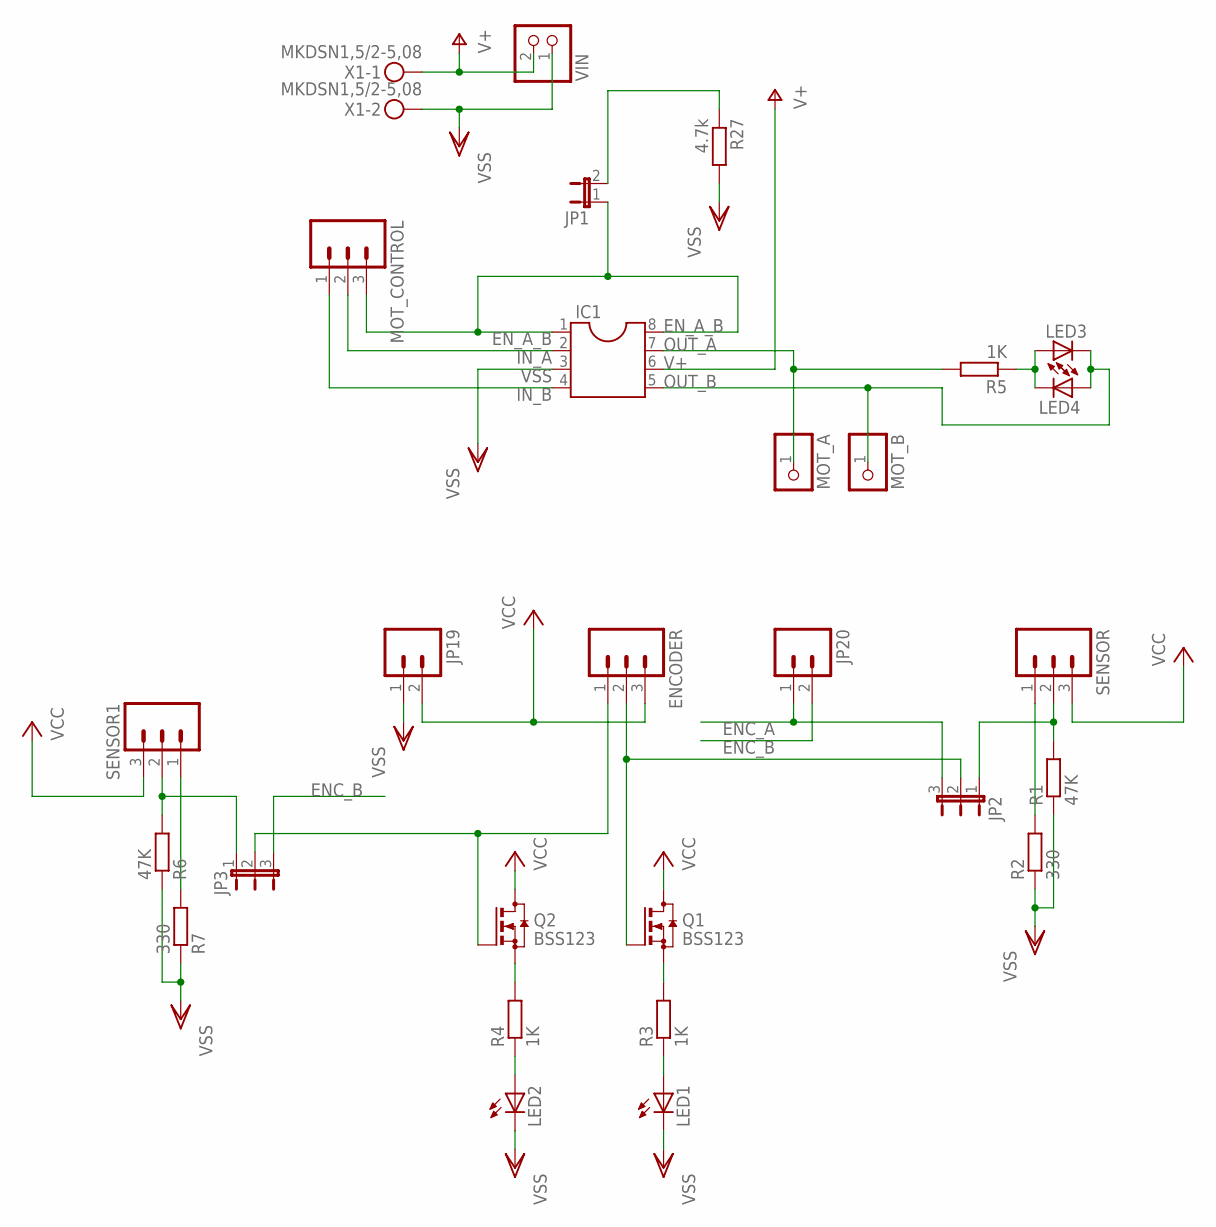
[picture p55: schematic ARE_moduls.sch, sheet 1, Motor Pololu encoder/driver]

Parts:
ENCODER: M03PTH; 1X03
IC1: DIL8S; SOCKET-08
JP1: JP1E; JP1
JP2, JP3: JP2E; JP2
JP19, JP20: M02PTH; 1X02
LED1, LED2, LED3, LED4: LEDCHIPLED_0805; CHIPLED_0805
MOT_A: PINHD-1X1; 1X01
MOT_B: PINHD-1X1; 1X01
MOT_CONTROL: M03PTH; 1X03
Q1, Q2: BSS123; SOT23
R1, R6: 47K; M0805
R2, R7: 330; M0805
R3, R4, R5: 1K; M0805
R27: 4.7k; R0805
SENSOR, SENSOR1: M03PTH; 1X03
VIN: PINHD-1X2; 1X02
X1: MKDSN1,5/2-5,08

Connections:
ENC_A: JP2.3, JP20.1
ENC_B: JP3.3, JP20.2
EN_A_B: IC1.1, IC1.8, JP1.1, MOT_CONTROL.3
IN_A: IC1.2, MOT_CONTROL.2
IN_B: IC1.4, MOT_CONTROL.1
unnamed: JP1.2, R27.1
unnamed: R2.2, SENSOR.1
unnamed: ENCODER.2, JP2.2, Q1.1 (G)
unnamed: JP2.1, R1.2, SENSOR.2
unnamed: Q1.2 (S), R3.2
unnamed: LED1.A, R3.1
unnamed: Q2.2 (S), R4.2
unnamed: LED2.A, R4.1
unnamed: LED3.A, LED4.C, R5.1
unnamed: R7.2, SENSOR1.1
unnamed: JP3.1, R6.2, SENSOR1.2
unnamed: ENCODER.1, JP3.2, Q2.1 (G)
OUT_A: IC1.7, MOT_A.1, R5.2
OUT_B: IC1.5, LED3.C, LED4.A, MOT_B.1
V+: IC1.6, VIN.2, X1.1
VCC: ENCODER.3, JP19.2, Q1.3 (D), Q2.3 (D), SENSOR.3, SENSOR1.3; also elsewhere on the board
VSS: IC1.3, JP19.1, LED1.C, LED2.C, R1.1, R2.1, R6.1, R7.1, R27.2, VIN.1, X1.2; also elsewhere on the board
