dragonet80/MultiMicro/Moduls/ARE_moduls.brd

## EAGLE design Moduls/ARE_moduls.brd (continued)

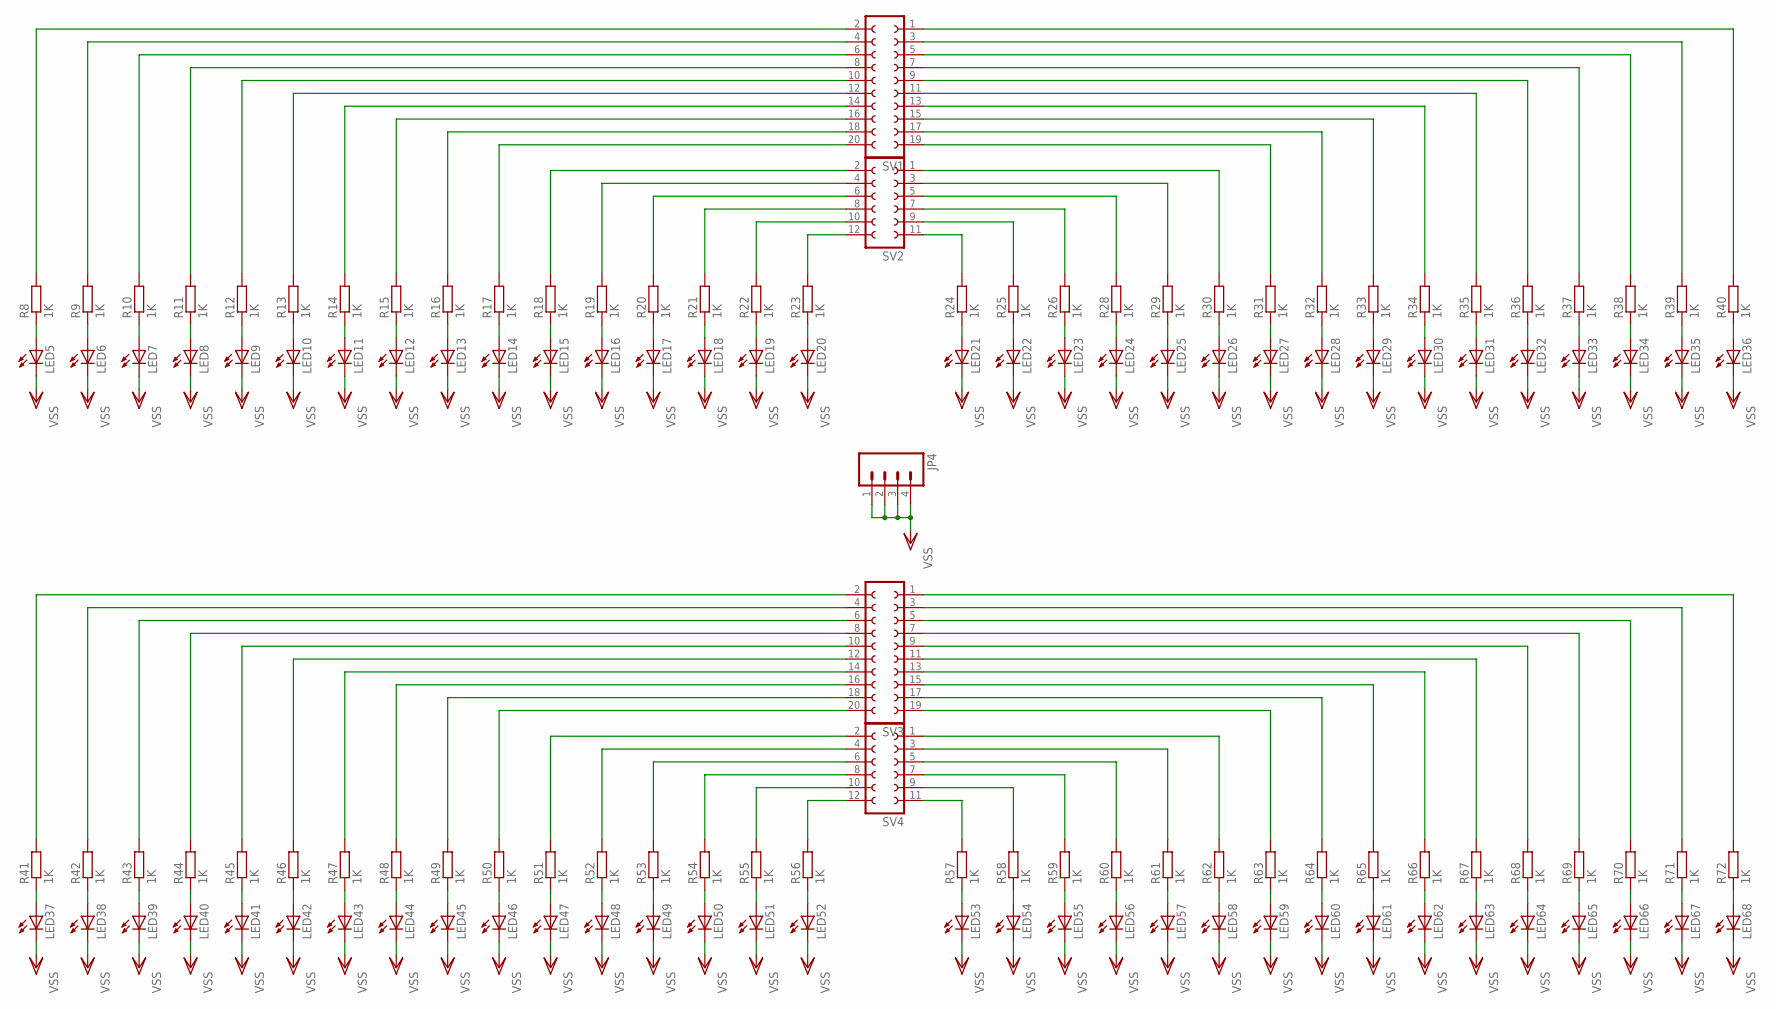
[picture p56: schematic ARE_moduls.sch, sheet 2, 4x 16 led]

Parts:
JP4: M04PTH; 1X04
LED5, LED6, LED7, LED8, LED9, LED10, LED11, LED12, LED13, LED14, LED15, LED16, LED17, LED18, LED19, LED20, LED21, LED22, LED23, LED24, LED25, LED26, LED27, LED28, LED29, LED30, LED31, LED32, LED33, LED34, LED35, LED36, LED37, LED38, LED39, LED40, LED41, LED42, LED43, LED44, LED45, LED46, LED47, LED48, LED49, LED50, LED51, LED52, LED53, LED54, LED55, LED56, LED57, LED58, LED59, LED60, LED61, LED62, LED63, LED64, LED65, LED66, LED67, LED68: LEDCHIPLED_0805; CHIPLED_0805
R8, R9, R10, R11, R12, R13, R14, R15, R16, R17, R18, R19, R20, R21, R22, R23, R24, R25, R26, R28, R29, R30, R31, R32, R33, R34, R35, R36, R37, R38, R39, R40, R41, R42, R43, R44, R45, R46, R47, R48, R49, R50, R51, R52, R53, R54, R55, R56, R57, R58, R59, R60, R61, R62, R63, R64, R65, R66, R67, R68, R69, R70, R71, R72: 1K; M0805
SV1, SV3: FE10-2
SV2, SV4: FE06-2

Connections:
unnamed: LED5.A, R8.1
unnamed: LED6.A, R9.1
unnamed: LED7.A, R10.1
unnamed: LED8.A, R11.1
unnamed: LED9.A, R12.1
unnamed: LED10.A, R13.1
unnamed: LED11.A, R14.1
unnamed: LED12.A, R15.1
unnamed: LED13.A, R16.1
unnamed: LED14.A, R17.1
unnamed: LED15.A, R18.1
unnamed: LED16.A, R19.1
unnamed: LED17.A, R20.1
unnamed: LED18.A, R21.1
unnamed: LED19.A, R22.1
unnamed: LED20.A, R23.1
unnamed: R23.2, SV2.12
unnamed: LED37.A, R41.1
unnamed: R22.2, SV2.10
unnamed: R21.2, SV2.8
unnamed: R20.2, SV2.6
unnamed: R19.2, SV2.4
unnamed: R18.2, SV2.2
unnamed: R17.2, SV1.20
unnamed: R16.2, SV1.18
unnamed: R15.2, SV1.16
unnamed: R14.2, SV1.14
unnamed: R13.2, SV1.12
unnamed: R12.2, SV1.10
unnamed: R11.2, SV1.8
unnamed: R10.2, SV1.6
unnamed: R9.2, SV1.4
unnamed: R8.2, SV1.2
unnamed: LED21.A, R24.1
unnamed: LED22.A, R25.1
unnamed: LED23.A, R26.1
unnamed: LED24.A, R28.1
unnamed: LED25.A, R29.1
unnamed: LED26.A, R30.1
unnamed: LED27.A, R31.1
unnamed: LED28.A, R32.1
unnamed: LED29.A, R33.1
unnamed: LED30.A, R34.1
unnamed: LED31.A, R35.1
unnamed: LED32.A, R36.1
unnamed: LED33.A, R37.1
unnamed: LED34.A, R38.1
unnamed: LED35.A, R39.1
unnamed: LED36.A, R40.1
unnamed: R24.2, SV2.11
unnamed: R25.2, SV2.9
unnamed: R26.2, SV2.7
unnamed: R28.2, SV2.5
unnamed: R29.2, SV2.3
unnamed: R30.2, SV2.1
unnamed: R31.2, SV1.19
unnamed: R32.2, SV1.17
unnamed: R33.2, SV1.15
unnamed: R34.2, SV1.13
unnamed: R35.2, SV1.11
unnamed: R36.2, SV1.9
unnamed: R37.2, SV1.7
unnamed: R38.2, SV1.5
unnamed: R39.2, SV1.3
unnamed: R40.2, SV1.1
unnamed: LED38.A, R42.1
unnamed: LED39.A, R43.1
unnamed: LED40.A, R44.1
unnamed: LED41.A, R45.1
unnamed: LED42.A, R46.1
unnamed: LED43.A, R47.1
unnamed: LED44.A, R48.1
unnamed: LED45.A, R49.1
unnamed: LED46.A, R50.1
unnamed: LED47.A, R51.1
unnamed: LED48.A, R52.1
unnamed: LED49.A, R53.1
unnamed: LED50.A, R54.1
unnamed: LED51.A, R55.1
unnamed: LED52.A, R56.1
unnamed: R56.2, SV4.12
unnamed: R55.2, SV4.10
unnamed: R54.2, SV4.8
unnamed: R53.2, SV4.6
unnamed: R52.2, SV4.4
unnamed: R51.2, SV4.2
unnamed: R50.2, SV3.20
unnamed: R49.2, SV3.18
unnamed: R48.2, SV3.16
unnamed: R47.2, SV3.14
unnamed: R46.2, SV3.12
unnamed: R45.2, SV3.10
unnamed: R44.2, SV3.8
unnamed: R43.2, SV3.6
unnamed: R42.2, SV3.4
unnamed: R41.2, SV3.2
unnamed: LED53.A, R57.1
unnamed: LED54.A, R58.1
unnamed: LED55.A, R59.1
unnamed: LED56.A, R60.1
unnamed: LED57.A, R61.1
unnamed: LED58.A, R62.1
unnamed: LED59.A, R63.1
unnamed: LED60.A, R64.1
unnamed: LED61.A, R65.1
unnamed: LED62.A, R66.1
unnamed: LED63.A, R67.1
unnamed: LED64.A, R68.1
unnamed: LED65.A, R69.1
unnamed: LED66.A, R70.1
unnamed: LED67.A, R71.1
unnamed: LED68.A, R72.1
unnamed: R57.2, SV4.11
unnamed: R58.2, SV4.9
unnamed: R59.2, SV4.7
unnamed: R60.2, SV4.5
unnamed: R61.2, SV4.3
unnamed: R62.2, SV4.1
unnamed: R63.2, SV3.19
unnamed: R64.2, SV3.17
unnamed: R65.2, SV3.15
unnamed: R66.2, SV3.13
unnamed: R67.2, SV3.11
unnamed: R68.2, SV3.9
unnamed: R69.2, SV3.7
unnamed: R70.2, SV3.5
unnamed: R71.2, SV3.3
unnamed: R72.2, SV3.1
VSS: JP4.1, JP4.2, JP4.3, JP4.4, LED5.C, LED6.C, LED7.C, LED8.C, LED9.C, LED10.C, LED11.C, LED12.C, LED13.C, LED14.C, LED15.C, LED16.C, LED17.C, LED18.C, LED19.C, LED20.C, LED21.C, LED22.C, LED23.C, LED24.C, LED25.C, LED26.C, LED27.C, LED28.C, LED29.C, LED30.C, LED31.C, LED32.C, LED33.C, LED34.C, LED35.C, LED36.C, LED37.C, LED38.C, LED39.C, LED40.C, LED41.C, LED42.C, LED43.C, LED44.C, LED45.C, LED46.C, LED47.C, LED48.C, LED49.C, LED50.C, LED51.C, LED52.C, LED53.C, LED54.C, LED55.C, LED56.C, LED57.C, LED58.C, LED59.C, LED60.C, LED61.C, LED62.C, LED63.C, LED64.C, LED65.C, LED66.C, LED67.C, LED68.C; also elsewhere on the board

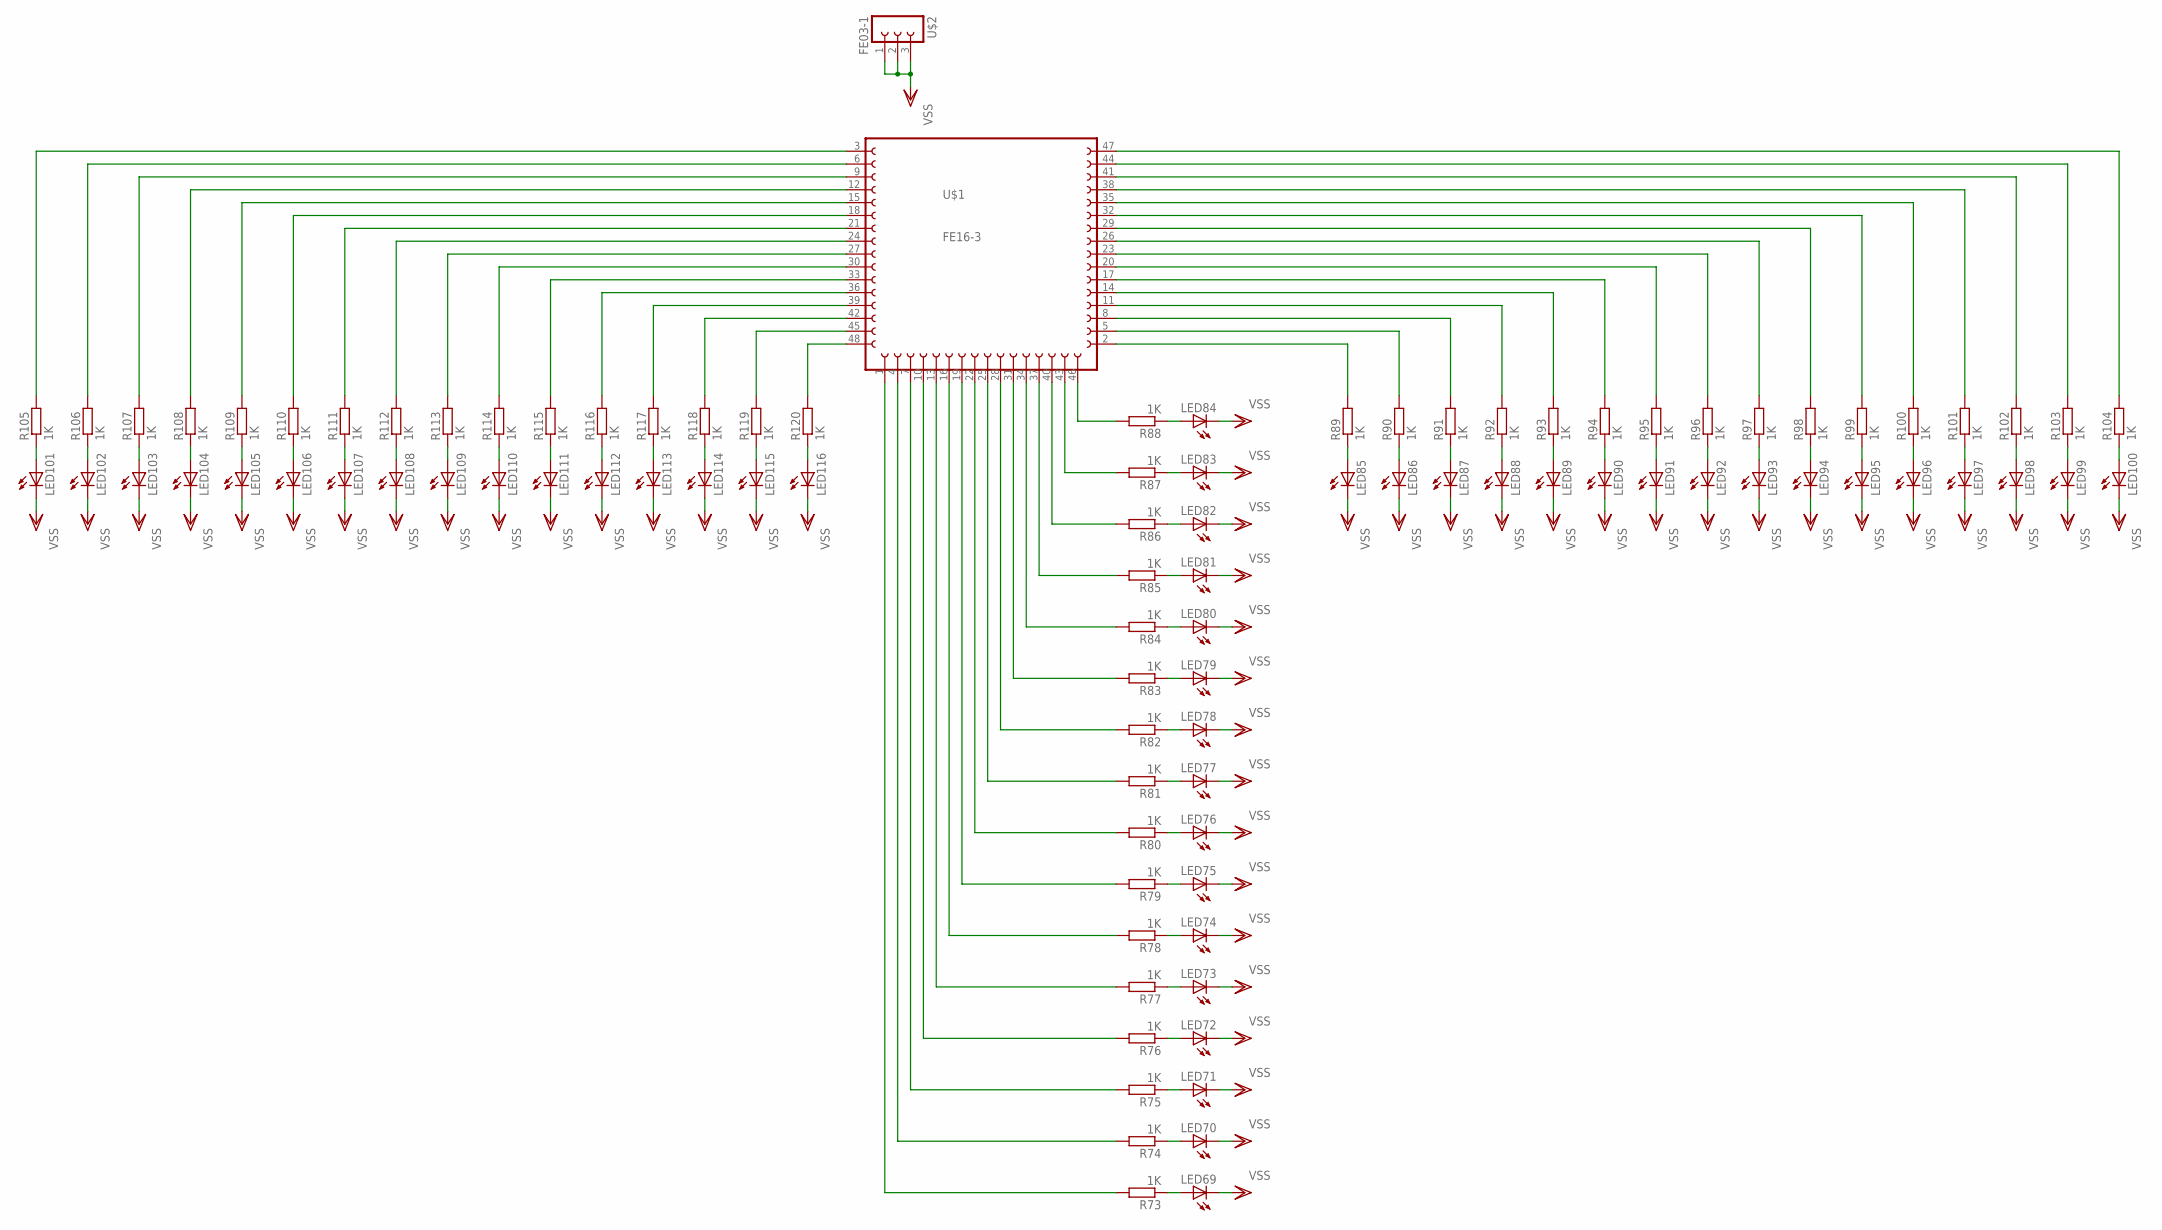
[picture p57: schematic ARE_moduls.sch, sheet 3, 3x 16 led]

Parts:
LED69, LED70, LED71, LED72, LED73, LED74, LED75, LED76, LED77, LED78, LED79, LED80, LED81, LED82, LED83, LED84, LED85, LED86, LED87, LED88, LED89, LED90, LED91, LED92, LED93, LED94, LED95, LED96, LED97, LED98, LED99, LED100, LED101, LED102, LED103, LED104, LED105, LED106, LED107, LED108, LED109, LED110, LED111, LED112, LED113, LED114, LED115, LED116: LEDCHIPLED_0805; CHIPLED_0805
R73, R74, R75, R76, R77, R78, R79, R80, R81, R82, R83, R84, R85, R86, R87, R88, R89, R90, R91, R92, R93, R94, R95, R96, R97, R98, R99, R100, R101, R102, R103, R104, R105, R106, R107, R108, R109, R110, R111, R112, R113, R114, R115, R116, R117, R118, R119, R120: 1K; M0805
U$1: FE16-3
U$2: FE03-1

Connections:
unnamed: LED69.A, R73.1
unnamed: LED70.A, R74.1
unnamed: LED71.A, R75.1
unnamed: LED72.A, R76.1
unnamed: LED73.A, R77.1
unnamed: LED74.A, R78.1
unnamed: LED75.A, R79.1
unnamed: LED76.A, R80.1
unnamed: LED77.A, R81.1
unnamed: LED78.A, R82.1
unnamed: LED79.A, R83.1
unnamed: LED80.A, R84.1
unnamed: LED81.A, R85.1
unnamed: LED82.A, R86.1
unnamed: LED83.A, R87.1
unnamed: LED84.A, R88.1
unnamed: R88.2, U$1.46
unnamed: R87.2, U$1.43
unnamed: R86.2, U$1.40
unnamed: R85.2, U$1.37
unnamed: R84.2, U$1.34
unnamed: R83.2, U$1.31
unnamed: R82.2, U$1.28
unnamed: R81.2, U$1.25
unnamed: R80.2, U$1.22
unnamed: R79.2, U$1.19
unnamed: R78.2, U$1.16
unnamed: R77.2, U$1.13
unnamed: R76.2, U$1.10
unnamed: R75.2, U$1.7
unnamed: R74.2, U$1.4
unnamed: R73.2, U$1.1
unnamed: LED85.A, R89.1
unnamed: LED86.A, R90.1
unnamed: LED87.A, R91.1
unnamed: LED88.A, R92.1
unnamed: LED89.A, R93.1
unnamed: LED90.A, R94.1
unnamed: LED91.A, R95.1
unnamed: LED92.A, R96.1
unnamed: LED93.A, R97.1
unnamed: LED94.A, R98.1
unnamed: LED95.A, R99.1
unnamed: LED96.A, R100.1
unnamed: LED97.A, R101.1
unnamed: LED98.A, R102.1
unnamed: LED99.A, R103.1
unnamed: LED100.A, R104.1
unnamed: R89.2, U$1.2
unnamed: R90.2, U$1.5
unnamed: R91.2, U$1.8
unnamed: R92.2, U$1.11
unnamed: R93.2, U$1.14
unnamed: R94.2, U$1.17
unnamed: R95.2, U$1.20
unnamed: R96.2, U$1.23
unnamed: R97.2, U$1.26
unnamed: R98.2, U$1.29
unnamed: R99.2, U$1.32
unnamed: R100.2, U$1.35
unnamed: R101.2, U$1.38
unnamed: R102.2, U$1.41
unnamed: R103.2, U$1.44
unnamed: R104.2, U$1.47
unnamed: LED101.A, R105.1
unnamed: LED102.A, R106.1
unnamed: LED103.A, R107.1
unnamed: LED104.A, R108.1
unnamed: LED105.A, R109.1
unnamed: LED106.A, R110.1
unnamed: LED107.A, R111.1
unnamed: LED108.A, R112.1
unnamed: LED109.A, R113.1
unnamed: LED110.A, R114.1
unnamed: LED111.A, R115.1
unnamed: LED112.A, R116.1
unnamed: LED113.A, R117.1
unnamed: LED114.A, R118.1
unnamed: LED115.A, R119.1
unnamed: LED116.A, R120.1
unnamed: R120.2, U$1.48
unnamed: R119.2, U$1.45
unnamed: R118.2, U$1.42
unnamed: R117.2, U$1.39
unnamed: R116.2, U$1.36
unnamed: R115.2, U$1.33
unnamed: R114.2, U$1.30
unnamed: R113.2, U$1.27
unnamed: R112.2, U$1.24
unnamed: R111.2, U$1.21
unnamed: R110.2, U$1.18
unnamed: R109.2, U$1.15
unnamed: R108.2, U$1.12
unnamed: R107.2, U$1.9
unnamed: R106.2, U$1.6
unnamed: R105.2, U$1.3
VSS: LED69.C, LED70.C, LED71.C, LED72.C, LED73.C, LED74.C, LED75.C, LED76.C, LED77.C, LED78.C, LED79.C, LED80.C, LED81.C, LED82.C, LED83.C, LED84.C, LED85.C, LED86.C, LED87.C, LED88.C, LED89.C, LED90.C, LED91.C, LED92.C, LED93.C, LED94.C, LED95.C, LED96.C, LED97.C, LED98.C, LED99.C, LED100.C, LED101.C, LED102.C, LED103.C, LED104.C, LED105.C, LED106.C, LED107.C, LED108.C, LED109.C, LED110.C, LED111.C, LED112.C, LED113.C, LED114.C, LED115.C, LED116.C, U$2.1, U$2.2, U$2.3; also elsewhere on the board

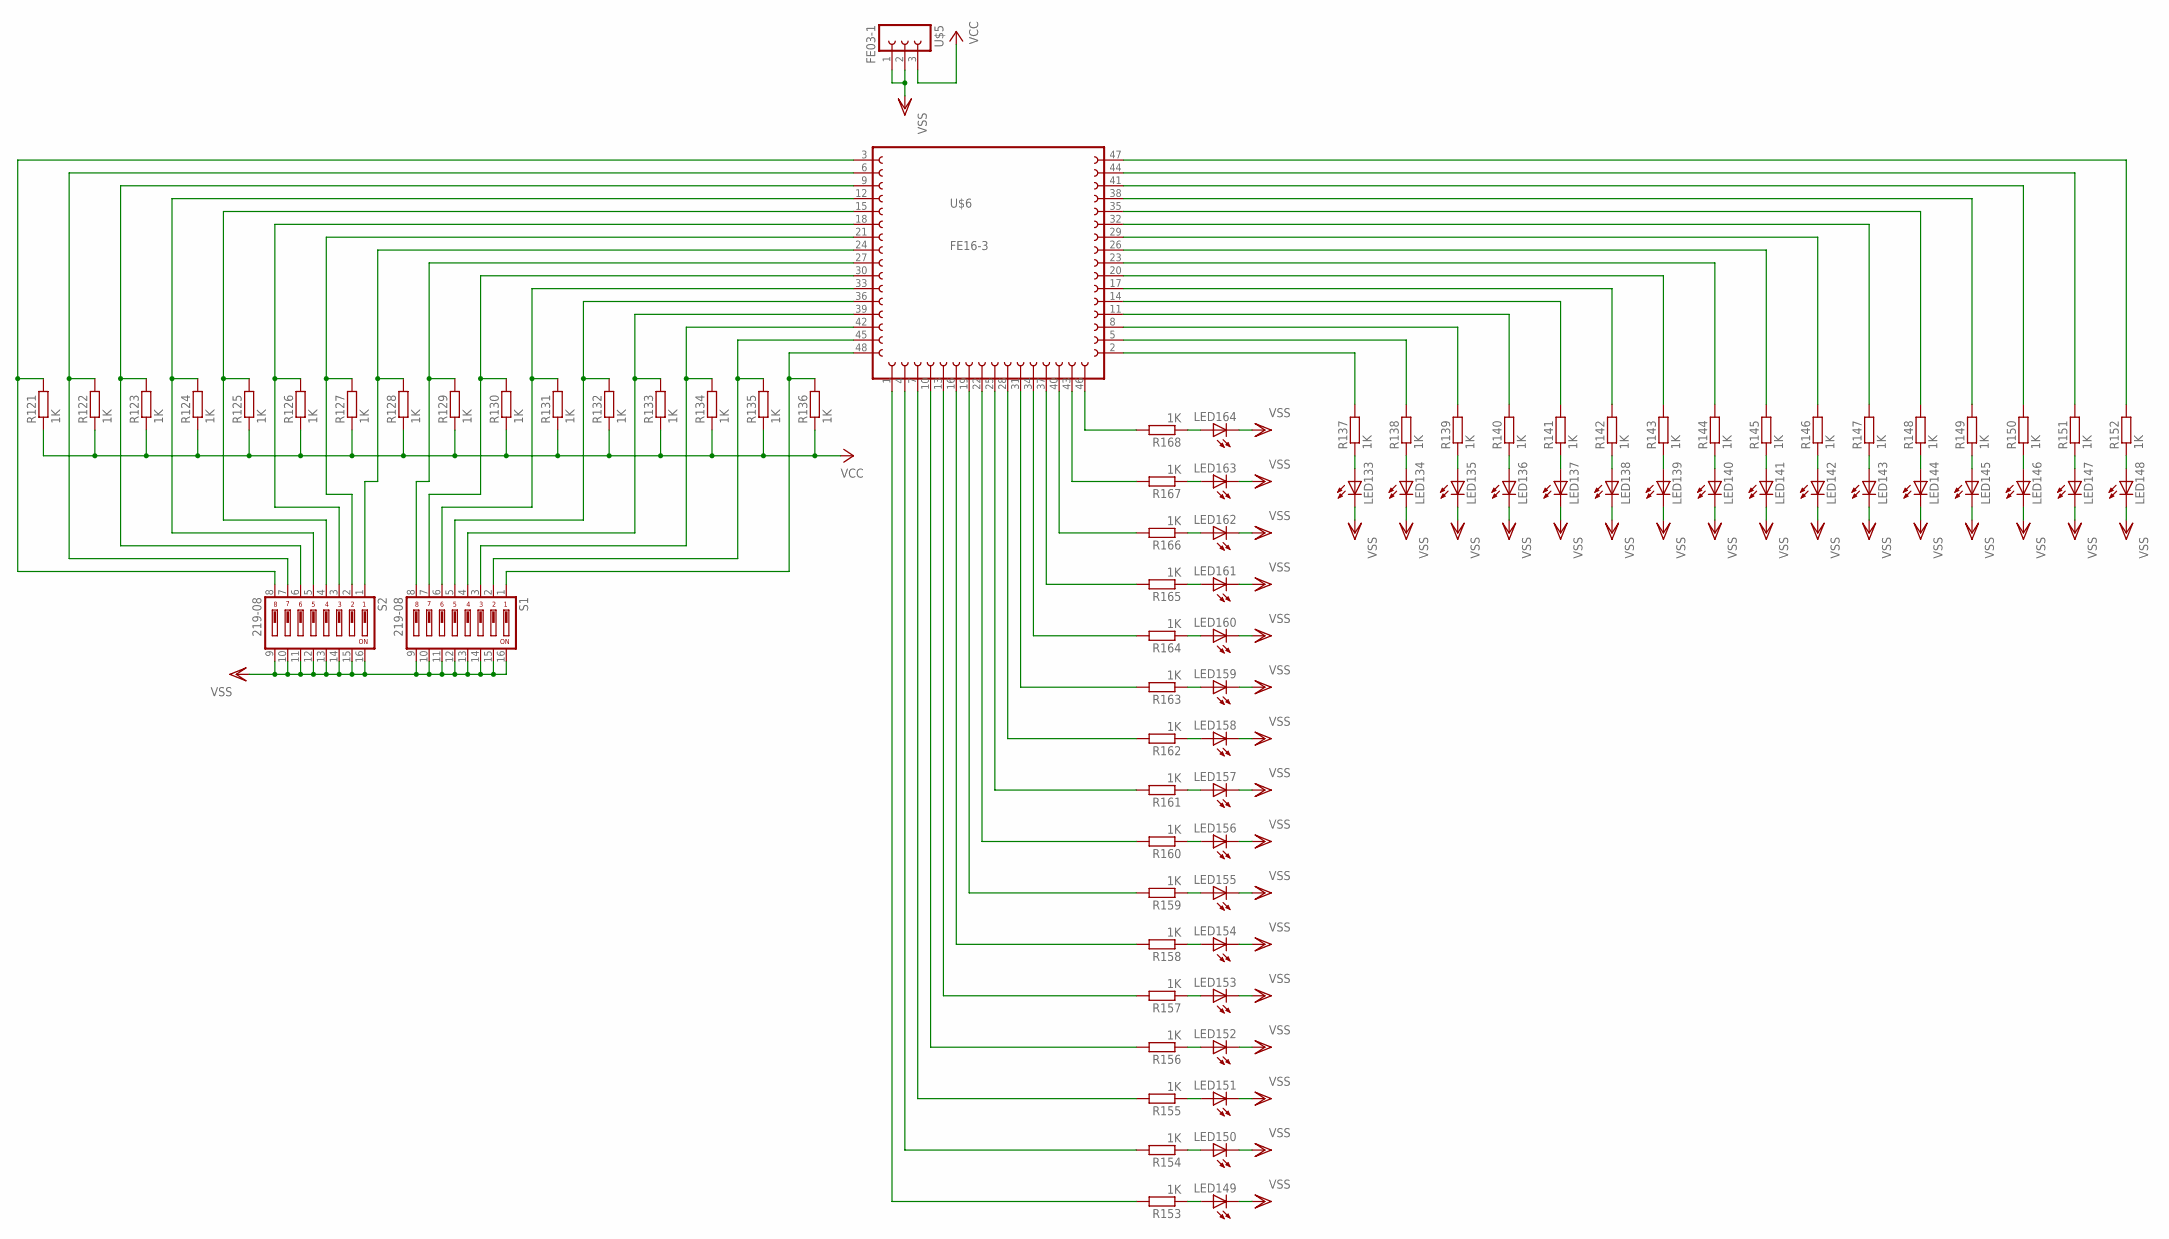
[picture p58: schematic ARE_moduls.sch, sheet 4, 2x 16 led + 16 dip-switch]

Parts:
LED133, LED134, LED135, LED136, LED137, LED138, LED139, LED140, LED141, LED142, LED143, LED144, LED145, LED146, LED147, LED148, LED149, LED150, LED151, LED152, LED153, LED154, LED155, LED156, LED157, LED158, LED159, LED160, LED161, LED162, LED163, LED164: LEDCHIPLED_0805; CHIPLED_0805
R121, R122, R123, R124, R125, R126, R127, R128, R129, R130, R131, R132, R133, R134, R135, R136, R137, R138, R139, R140, R141, R142, R143, R144, R145, R146, R147, R148, R149, R150, R151, R152, R153, R154, R155, R156, R157, R158, R159, R160, R161, R162, R163, R164, R165, R166, R167, R168: 1K; M0805
S1, S2: 219-08; CTS-219-08
U$5: FE03-1
U$6: FE16-3

Connections:
unnamed: R135.2, S1.2, U$6.45
unnamed: R136.2, S1.1, U$6.48
unnamed: R134.2, S1.3, U$6.42
unnamed: R133.2, S1.4, U$6.39
unnamed: R132.2, S1.5, U$6.36
unnamed: R131.2, S1.6, U$6.33
unnamed: R130.2, S1.7, U$6.30
unnamed: R129.2, S1.8, U$6.27
unnamed: R128.2, S2.1, U$6.24
unnamed: R127.2, S2.2, U$6.21
unnamed: R126.2, S2.3, U$6.18
unnamed: R125.2, S2.4, U$6.15
unnamed: R124.2, S2.5, U$6.12
unnamed: R123.2, S2.6, U$6.9
unnamed: R122.2, S2.7, U$6.6
unnamed: R121.2, S2.8, U$6.3
unnamed: LED133.A, R137.1
unnamed: LED134.A, R138.1
unnamed: LED135.A, R139.1
unnamed: LED136.A, R140.1
unnamed: LED137.A, R141.1
unnamed: LED138.A, R142.1
unnamed: LED139.A, R143.1
unnamed: LED140.A, R144.1
unnamed: LED141.A, R145.1
unnamed: LED142.A, R146.1
unnamed: LED143.A, R147.1
unnamed: LED144.A, R148.1
unnamed: LED145.A, R149.1
unnamed: LED146.A, R150.1
unnamed: LED147.A, R151.1
unnamed: LED148.A, R152.1
unnamed: R137.2, U$6.2
unnamed: R138.2, U$6.5
unnamed: R139.2, U$6.8
unnamed: R140.2, U$6.11
unnamed: R141.2, U$6.14
unnamed: R142.2, U$6.17
unnamed: R143.2, U$6.20
unnamed: R144.2, U$6.23
unnamed: R145.2, U$6.26
unnamed: R146.2, U$6.29
unnamed: R147.2, U$6.32
unnamed: R148.2, U$6.35
unnamed: R149.2, U$6.38
unnamed: R150.2, U$6.41
unnamed: R151.2, U$6.44
unnamed: R152.2, U$6.47
unnamed: LED149.A, R153.1
unnamed: LED150.A, R154.1
unnamed: LED151.A, R155.1
unnamed: LED152.A, R156.1
unnamed: LED153.A, R157.1
unnamed: LED154.A, R158.1
unnamed: LED155.A, R159.1
unnamed: LED156.A, R160.1
unnamed: LED157.A, R161.1
unnamed: LED158.A, R162.1
unnamed: LED159.A, R163.1
unnamed: LED160.A, R164.1
unnamed: LED161.A, R165.1
unnamed: LED162.A, R166.1
unnamed: LED163.A, R167.1
unnamed: LED164.A, R168.1
unnamed: R168.2, U$6.46
unnamed: R167.2, U$6.43
unnamed: R166.2, U$6.40
unnamed: R165.2, U$6.37
unnamed: R164.2, U$6.34
unnamed: R163.2, U$6.31
unnamed: R162.2, U$6.28
unnamed: R161.2, U$6.25
unnamed: R160.2, U$6.22
unnamed: R159.2, U$6.19
unnamed: R158.2, U$6.16
unnamed: R157.2, U$6.13
unnamed: R156.2, U$6.10
unnamed: R155.2, U$6.7
unnamed: R154.2, U$6.4
unnamed: R153.2, U$6.1
VCC: R121.1, R122.1, R123.1, R124.1, R125.1, R126.1, R127.1, R128.1, R129.1, R130.1, R131.1, R132.1, R133.1, R134.1, R135.1, R136.1, U$5.3; also elsewhere on the board
VSS: LED133.C, LED134.C, LED135.C, LED136.C, LED137.C, LED138.C, LED139.C, LED140.C, LED141.C, LED142.C, LED143.C, LED144.C, LED145.C, LED146.C, LED147.C, LED148.C, LED149.C, LED150.C, LED151.C, LED152.C, LED153.C, LED154.C, LED155.C, LED156.C, LED157.C, LED158.C, LED159.C, LED160.C, LED161.C, LED162.C, LED163.C, LED164.C, S1.9, S1.10, S1.11, S1.12, S1.13, S1.14, S1.15, S1.16, S2.9, S2.10, S2.11, S2.12, S2.13, S2.14, S2.15, S2.16, U$5.1, U$5.2; also elsewhere on the board

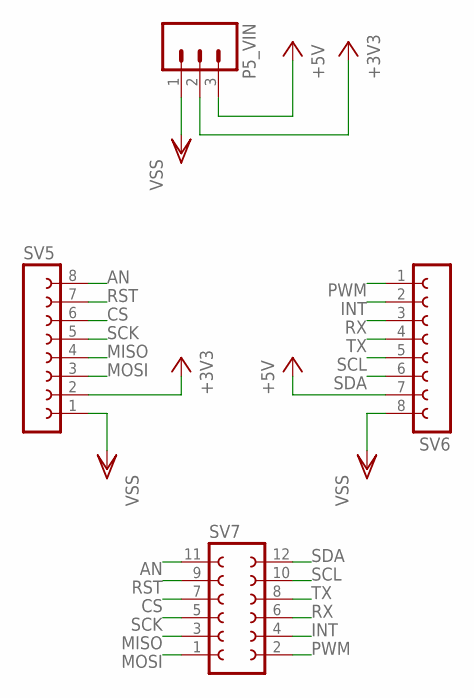
[picture p59: schematic ARE_moduls.sch, sheet 5, Adaptador Click]

Parts:
P5_VIN: M03PTH; 1X03
SV5, SV6: FE08-1; FE08
SV7: FE06-2

Connections:
+3V3: P5_VIN.2, SV5.2; also elsewhere on the board
+5V: P5_VIN.3, SV6.7; also elsewhere on the board
AN: SV5.8, SV7.11
CS: SV5.6, SV7.7
INT: SV6.2, SV7.4
MISO: SV5.4, SV7.3
MOSI: SV5.3, SV7.1
PWM: SV6.1, SV7.2
RST: SV5.7, SV7.9
RX: SV6.3, SV7.6
SCK: SV5.5, SV7.5
SCL: SV6.5, SV7.10
SDA: SV6.6, SV7.12
TX: SV6.4, SV7.8
VSS: P5_VIN.1, SV5.1, SV6.8; also elsewhere on the board

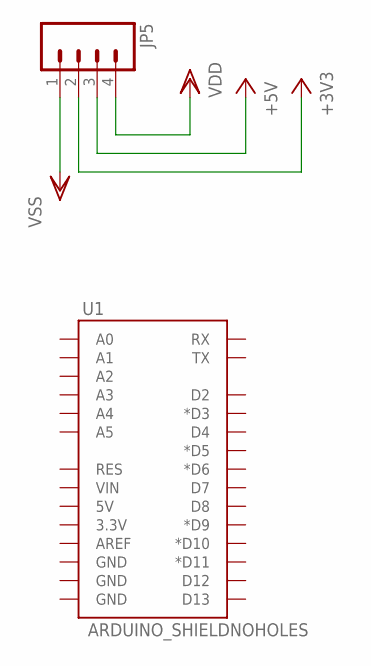
[picture p60: schematic ARE_moduls.sch, sheet 6, Arduino Shield]

Parts:
JP5: M04PTH; 1X04
U1: ARDUINO_SHIELDNOHOLES; DUEMILANOVE_SHIELD_NOHOLES

Connections:
+3V3: JP5.2; also elsewhere on the board
+5V: JP5.3; also elsewhere on the board
VDD: JP5.4
VSS: JP5.1; also elsewhere on the board

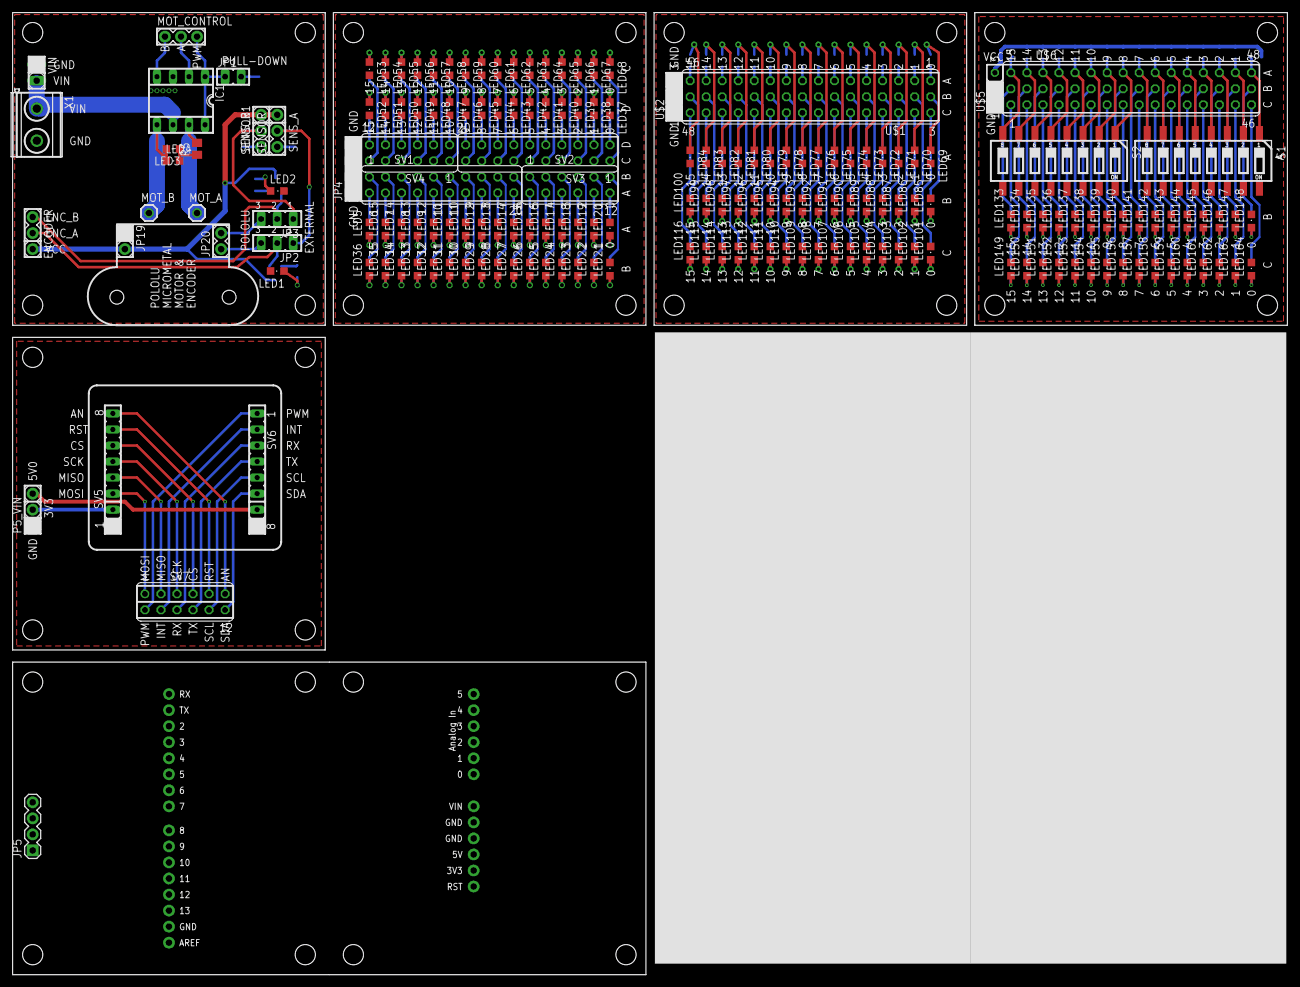
[picture p61: board ARE_moduls.brd from above]

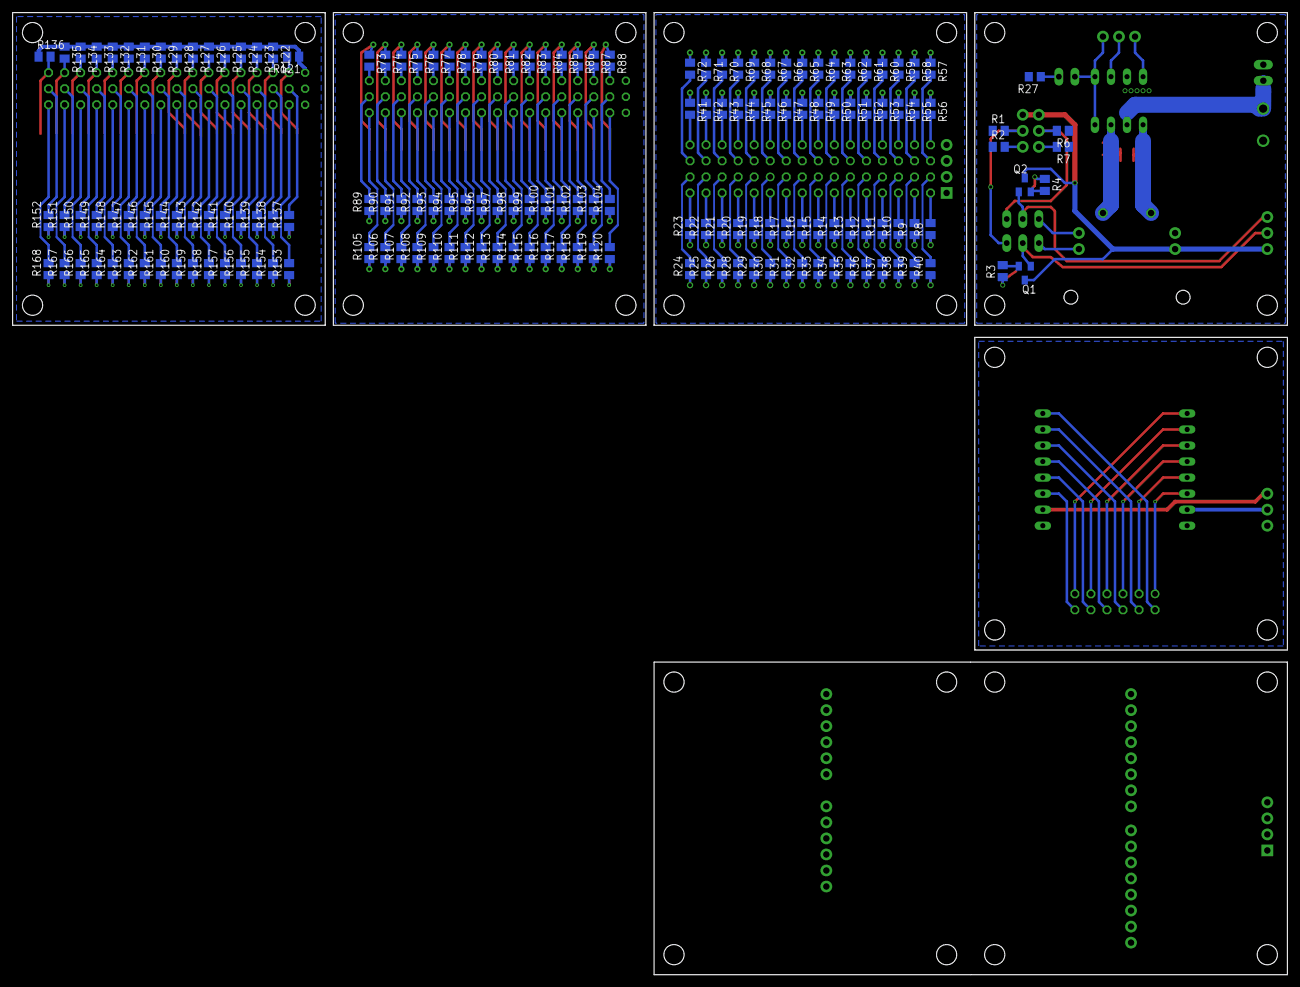
[picture p62: board ARE_moduls.brd from below]

Board: 2 copper layers, 201.9 x 152.4 mm, 349 parts (169 on the bottom side), 340 nets.
